schlae/cm5-reveng/BCM2712_HS.kicad_sch

## KiCad design BCM2712_HS.kicad_sch (2025-08-24)

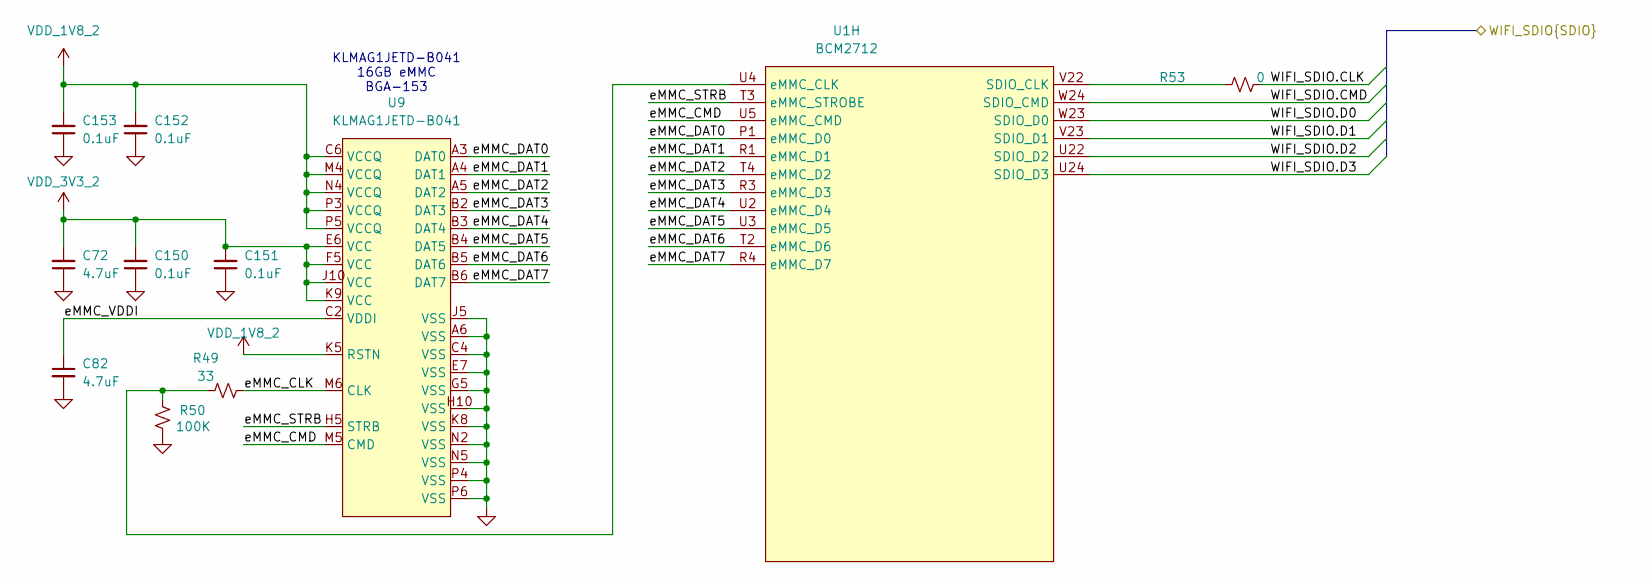
[picture p17: schematic BCM2712_HS.kicad_sch]

Parts:
C72, C82: 4.7uF; C_0402_1005Metric
C150, C151, C152, C153: 0.1uF; C_0201_0603Metric
R49: 33; R_0201_0603Metric
R50: 100K; R_0201_0603Metric
R53: 0; R_0201_0603Metric
U1: BCM2712; BGA-586_25x25_17.0x17.0mm
U9: KLMAG1JETD-B041; LFBGA-153_11.5x13mm_Layout14x14_P0.5mm

Connections:
GND: C72.1, C82.2, C150.1, C151.1, C152.1, C153.1, R50.2, U9.A6 (VSS), U9.C4 (VSS), U9.E7 (VSS), U9.G5 (VSS), U9.H10 (VSS), U9.J5 (VSS), U9.K8 (VSS), U9.N2 (VSS), U9.N5 (VSS), U9.P4 (VSS), U9.P6 (VSS)
unnamed: R49.2, R50.1, U1.U4 (eMMC_CLK)
unnamed: R53.1, U1.V22 (SDIO_CLK)
VDD_1V8_2: C152.2, C153.2, U9.C6 (VCCQ), U9.K5 (RSTN), U9.M4 (VCCQ), U9.N4 (VCCQ), U9.P3 (VCCQ), U9.P5 (VCCQ)
VDD_3V3_2: C72.2, C150.2, C151.2, U9.E6 (VCC), U9.F5 (VCC), U9.J10 (VCC), U9.K9 (VCC)
WIFI_SDIO.CLK: R53.2
WIFI_SDIO.CMD: U1.W24 (SDIO_CMD)
WIFI_SDIO.D0: U1.W23 (SDIO_D0)
WIFI_SDIO.D1: U1.V23 (SDIO_D1)
WIFI_SDIO.D2: U1.U22 (SDIO_D2)
WIFI_SDIO.D3: U1.U24 (SDIO_D3)
eMMC_CLK: R49.1, U9.M6 (CLK)
eMMC_CMD: U1.U5 (eMMC_CMD), U9.M5 (CMD)
eMMC_DAT0: U1.P1 (eMMC_D0), U9.A3 (DAT0)
eMMC_DAT1: U1.R1 (eMMC_D1), U9.A4 (DAT1)
eMMC_DAT2: U1.T4 (eMMC_D2), U9.A5 (DAT2)
eMMC_DAT3: U1.R3 (eMMC_D3), U9.B2 (DAT3)
eMMC_DAT4: U1.U2 (eMMC_D4), U9.B3 (DAT4)
eMMC_DAT5: U1.U3 (eMMC_D5), U9.B4 (DAT5)
eMMC_DAT6: U1.T2 (eMMC_D6), U9.B5 (DAT6)
eMMC_DAT7: U1.R4 (eMMC_D7), U9.B6 (DAT7)
eMMC_STRB: U1.T3 (eMMC_STROBE), U9.H5 (STRB)
eMMC_VDDI: C82.1, U9.C2 (VDDI)

Notes on the sheet:
KLMAG1JETD-B041 16GB eMMC BGA-153
