schlae/cm5-reveng/BCM2712_MISC.kicad_sch

## KiCad design BCM2712_MISC.kicad_sch (2025-08-24)

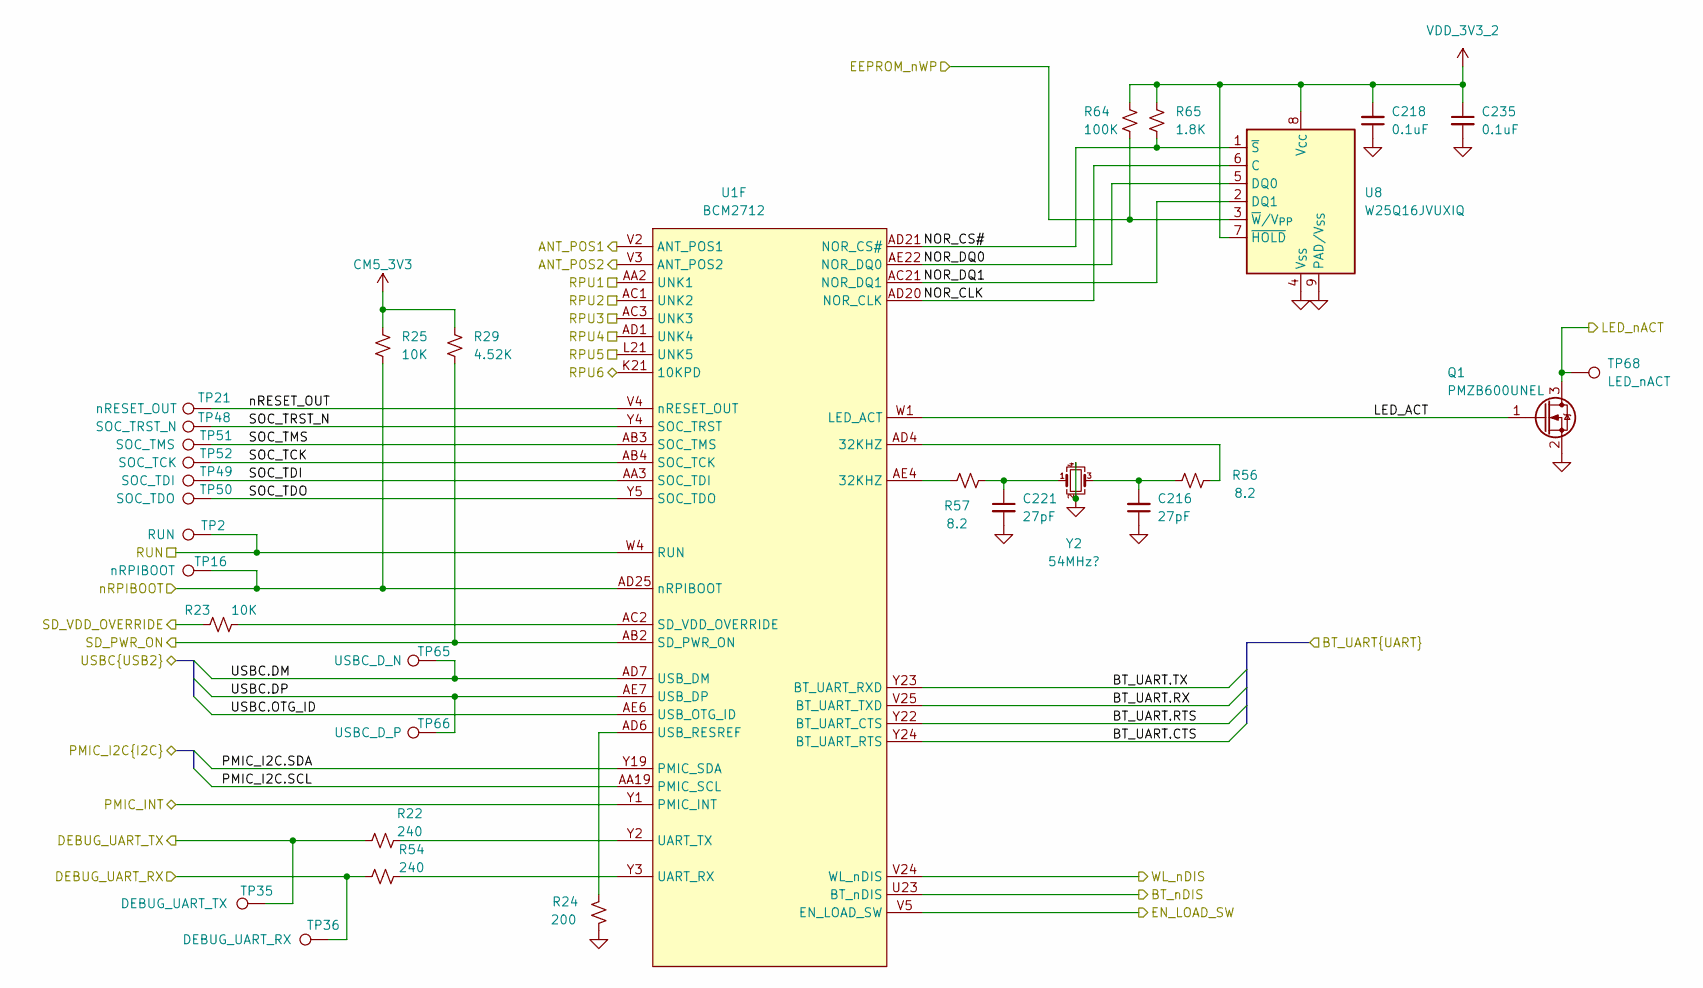
[picture p18: schematic BCM2712_MISC.kicad_sch]

Parts:
C216, C221: 27pF; C_0201_0603Metric
C218, C235: 0.1uF; C_0201_0603Metric
Q1: PMZB600UNEL; FEMTO_FET
R22, R54: 240; R_0201_0603Metric
R23, R25: 10K; R_0201_0603Metric
R24: 200; R_0201_0603Metric
R29: 4.52K; R_0201_0603Metric
R56, R57: 8.2; R_0201_0603Metric
R64: 100K; R_0201_0603Metric
R65: 1.8K; R_0201_0603Metric
TP2: RUN; TestPoint_Pad_D1.0mm
TP16: nRPIBOOT; TestPoint_Pad_D1.0mm
TP21: nRESET_OUT; TestPoint_Pad_D1.0mm
TP35: DEBUG_UART_TX; TestPoint_Pad_D1.0mm
TP36: DEBUG_UART_RX; TestPoint_Pad_D1.0mm
TP48: SOC_TRST_N; TestPoint_Pad_D1.0mm
TP49: SOC_TDI; TestPoint_Pad_D1.0mm
TP50: SOC_TDO; TestPoint_Pad_D1.0mm
TP51: SOC_TMS; TestPoint_Pad_D1.0mm
TP52: SOC_TCK; TestPoint_Pad_D1.0mm
TP65: USBC_D_N; TestPoint_Pad_D1.0mm
TP66: USBC_D_P; TestPoint_Pad_D1.0mm
TP68: LED_nACT; TestPoint_Pad_D1.0mm
U1: BCM2712; BGA-586_25x25_17.0x17.0mm
U8: W25Q16JVUXIQ; LFCSP-8-1EP_3x2mm_P0.5mm_EP1.6x0.25mm
Y2: 54MHz?; Oscillator_SMD_Abracon_ASE-4Pin_3.2x2.5mm

Connections:
ANT_POS1: U1.V2 (ANT_POS1)
ANT_POS2: U1.V3 (ANT_POS2)
BT_UART.CTS: U1.Y24 (BT_UART_RTS)
BT_UART.RTS: U1.Y22 (BT_UART_CTS)
BT_UART.RX: U1.V25 (BT_UART_TXD)
BT_UART.TX: U1.Y23 (BT_UART_RXD)
BT_nDIS: U1.U23 (BT_nDIS)
CM5_3V3: R25.1, R29.2
DEBUG_UART_RX: R54.1, TP36.1
DEBUG_UART_TX: R22.2, TP35.1
EEPROM_nWP: R64.1, U8.3 (~W/V_{PP})
EN_LOAD_SW: U1.V5 (EN_LOAD_SW)
GND: C216.1, C218.1, C221.2, C235.2, Q1.2 (S), R24.2, U8.4 (V_{SS}), U8.9 (PAD/V_{SS}), Y2.2, Y2.4
LED_ACT: Q1.1 (G), U1.W1 (LED_ACT)
LED_nACT: Q1.3 (D), TP68.1
NOR_CLK: U1.AD20 (NOR_CLK), U8.6 (C)
NOR_CS#: R65.1, U1.AD21 (NOR_CS#), U8.1 (~S)
NOR_DQ0: U1.AE22 (NOR_DQ0), U8.5 (DQ0)
NOR_DQ1: U1.AC21 (NOR_DQ1), U8.2 (DQ1)
unnamed: C216.2, R56.1, Y2.3
unnamed: C221.1, R57.1, Y2.1
unnamed: R22.1, U1.Y2 (UART_TX)
unnamed: R23.1, U1.AC2 (SD_VDD_OVERRIDE)
unnamed: R24.1, U1.AD6 (USB_RESREF)
unnamed: R54.2, U1.Y3 (UART_RX)
unnamed: R56.2, U1.AD4 (32KHZ)
unnamed: R57.2, U1.AE4 (32KHZ)
PMIC_I2C.SCL: U1.AA19 (PMIC_SCL)
PMIC_I2C.SDA: U1.Y19 (PMIC_SDA)
PMIC_INT: U1.Y1 (PMIC_INT)
RPU1: U1.AA2 (UNK1)
RPU2: U1.AC1 (UNK2)
RPU3: U1.AC3 (UNK3)
RPU4: U1.AD1 (UNK4)
RPU5: U1.L21 (UNK5)
RPU6: U1.K21 (10KPD)
RUN: TP2.1, U1.W4 (RUN)
SD_PWR_ON: R29.1, U1.AB2 (SD_PWR_ON)
SD_VDD_OVERRIDE: R23.2
SOC_TCK: TP52.1, U1.AB4 (SOC_TCK)
SOC_TDI: TP49.1, U1.AA3 (SOC_TDI)
SOC_TDO: TP50.1, U1.Y5 (SOC_TDO)
SOC_TMS: TP51.1, U1.AB3 (SOC_TMS)
SOC_TRST_N: TP48.1, U1.Y4 (SOC_TRST)
USBC.DM: TP65.1, U1.AD7 (USB_DM)
USBC.DP: TP66.1, U1.AE7 (USB_DP)
USBC.OTG_ID: U1.AE6 (USB_OTG_ID)
VDD_3V3_2: C218.2, C235.1, R64.2, R65.2, U8.7 (~HOLD), U8.8 (V_{CC})
WL_nDIS: U1.V24 (WL_nDIS)
nRESET_OUT: TP21.1, U1.V4 (nRESET_OUT)
nRPIBOOT: R25.2, TP16.1, U1.AD25 (nRPIBOOT)
