schlae/cm5-reveng/BCM2712_PWR2.kicad_sch

## KiCad design BCM2712_PWR2.kicad_sch (2025-08-24)

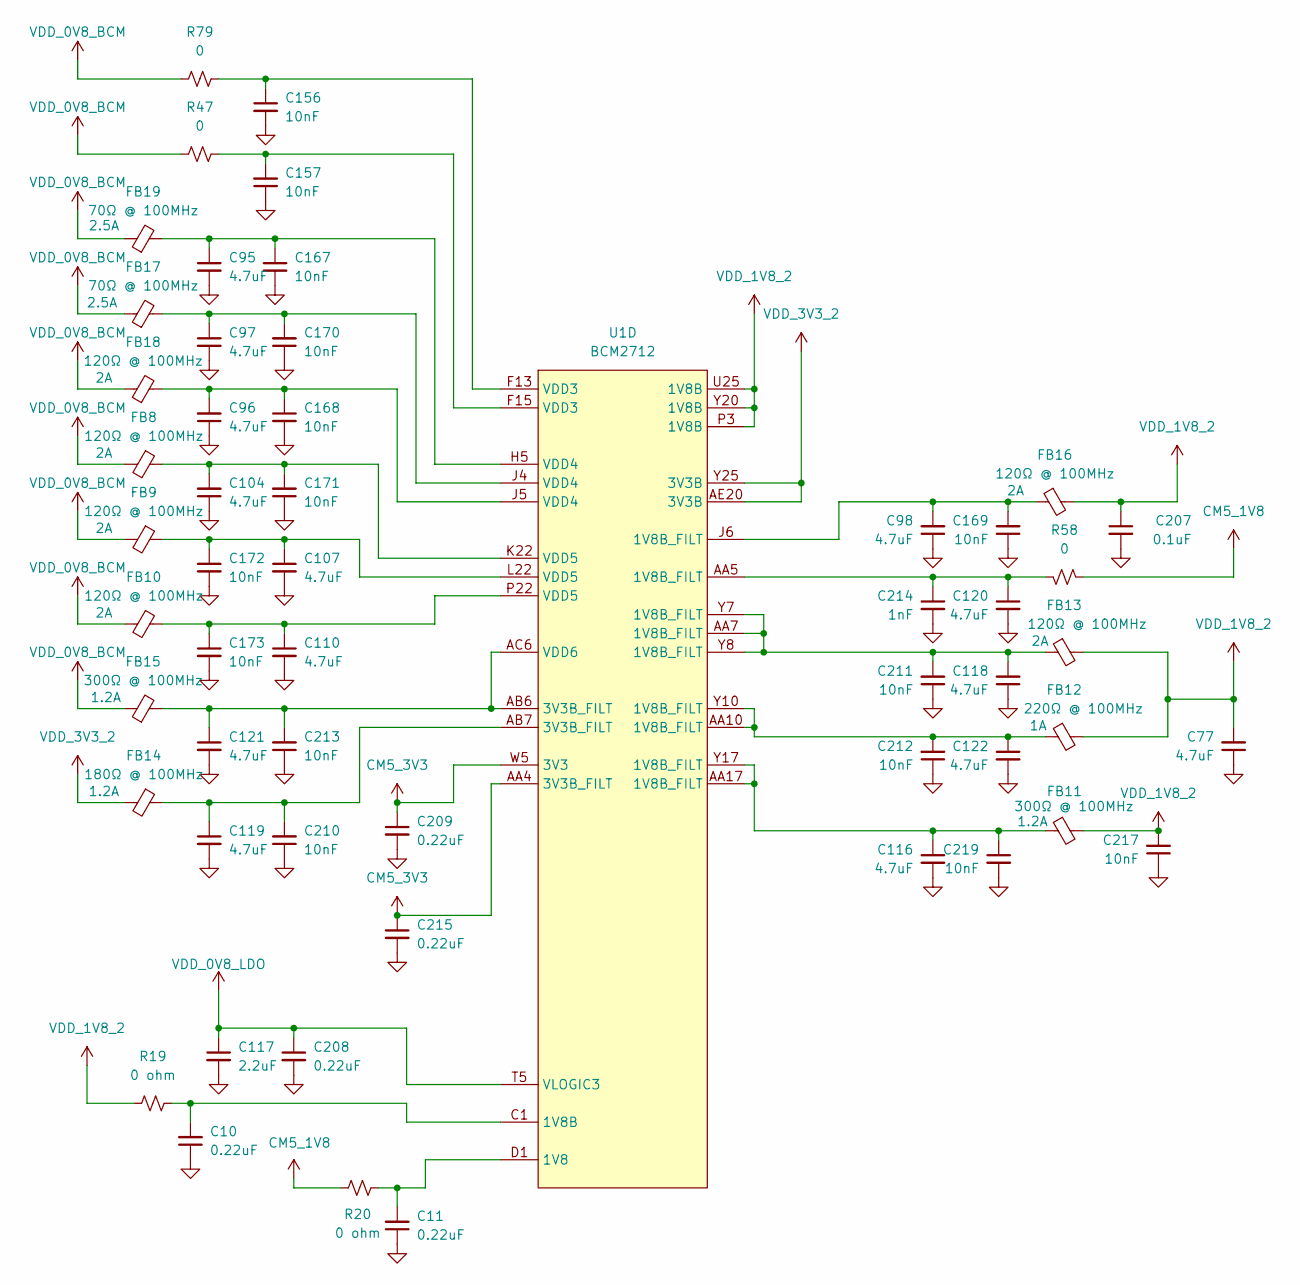
[picture p19: schematic BCM2712_PWR2.kicad_sch]

Parts:
C10, C11, C208, C209, C215: 0.22uF; C_0201_0603Metric
C77, C95, C96, C97, C98, C104, C107, C110, C116, C118, C119, C120, C121, C122: 4.7uF; C_0402_1005Metric
C117: 2.2uF; C_0402_1005Metric
C156, C157, C167, C168, C169, C170, C171, C172, C173, C210, C211, C212, C213, C217, C219: 10nF; C_0201_0603Metric
C207: 0.1uF; C_0201_0603Metric
C214: 1nF; C_0201_0603Metric
FB8, FB9, FB10, FB13, FB16, FB18: 120Ω @ 100MHz; L_0402_1005Metric; Rating 2A
FB11, FB15: 300Ω @ 100MHz; L_0402_1005Metric; Rating 1.2A
FB12: 220Ω @ 100MHz; L_0402_1005Metric; Rating 1A
FB14: 180Ω @ 100MHz; L_0402_1005Metric; Rating 1.2A
FB17, FB19: 70Ω @ 100MHz; L_0402_1005Metric; Rating 2.5A
R19, R20: 0 ohm; R_0201_0603Metric
R47, R58, R79: 0; R_0201_0603Metric
U1: BCM2712; BGA-586_25x25_17.0x17.0mm

Connections:
CM5_1V8: R20.2, R58.2
CM5_3V3: C209.1, C215.1, U1.AA4 (3V3B_FILT), U1.W5 (3V3)
GND: C10.1, C11.1, C77.1, C95.2, C96.1, C97.2, C98.1, C104.1, C107.2, C110.2, C116.2, C117.2, C118.1, C119.2, C120.2, C121.2, C122.2, C156.2, C157.1, C167.2, C168.2, C169.1, C170.1, C171.1, C172.2, C173.2, C207.2, C208.2, C209.2, C210.1, C211.1, C212.1, C213.1, C214.2, C215.2, C217.1, C219.2
unnamed: C10.2, R19.1, U1.C1 (1V8B)
unnamed: C11.2, R20.1, U1.D1 (1V8)
unnamed: C104.2, C171.2, FB8.1, U1.K22 (VDD5)
unnamed: C107.1, C172.1, FB9.1, U1.L22 (VDD5)
unnamed: C110.1, C173.1, FB10.1, U1.P22 (VDD5)
unnamed: C116.1, C219.1, FB11.1, U1.AA17 (1V8B_FILT), U1.Y17 (1V8B_FILT)
unnamed: C118.2, C211.2, FB13.1, U1.AA7 (1V8B_FILT), U1.Y7 (1V8B_FILT), U1.Y8 (1V8B_FILT)
unnamed: C119.1, C210.2, FB14.1, U1.AB7 (3V3B_FILT)
unnamed: C120.1, C214.1, R58.1, U1.AA5 (1V8B_FILT)
unnamed: C121.1, C213.2, FB15.2, U1.AB6 (3V3B_FILT), U1.AC6 (VDD6)
unnamed: C122.1, C212.2, FB12.1, U1.AA10 (1V8B_FILT), U1.Y10 (1V8B_FILT)
unnamed: C156.1, R79.1, U1.F13 (VDD3)
unnamed: C157.2, R47.1, U1.F15 (VDD3)
unnamed: C95.1, C167.1, FB19.2, U1.H5 (VDD4)
unnamed: C96.2, C168.1, FB18.2, U1.J5 (VDD4)
unnamed: C98.2, C169.2, FB16.1, U1.J6 (1V8B_FILT)
unnamed: C97.1, C170.2, FB17.2, U1.J4 (VDD4)
VDD_0V8_BCM: FB8.2, FB9.2, FB10.2, FB15.1, FB17.1, FB18.1, FB19.1, R47.2, R79.2
VDD_0V8_LDO: C117.1, C208.1, U1.T5 (VLOGIC3)
VDD_1V8_2: C77.2, C207.1, C217.2, FB11.2, FB12.2, FB13.2, FB16.2, R19.2, U1.P3 (1V8B), U1.U25 (1V8B), U1.Y20 (1V8B)
VDD_3V3_2: FB14.2, U1.AE20 (3V3B), U1.Y25 (3V3B)
