schlae/cm5-reveng/BCM2712_PWR.kicad_sch

## KiCad design BCM2712_PWR.kicad_sch (2025-08-24)

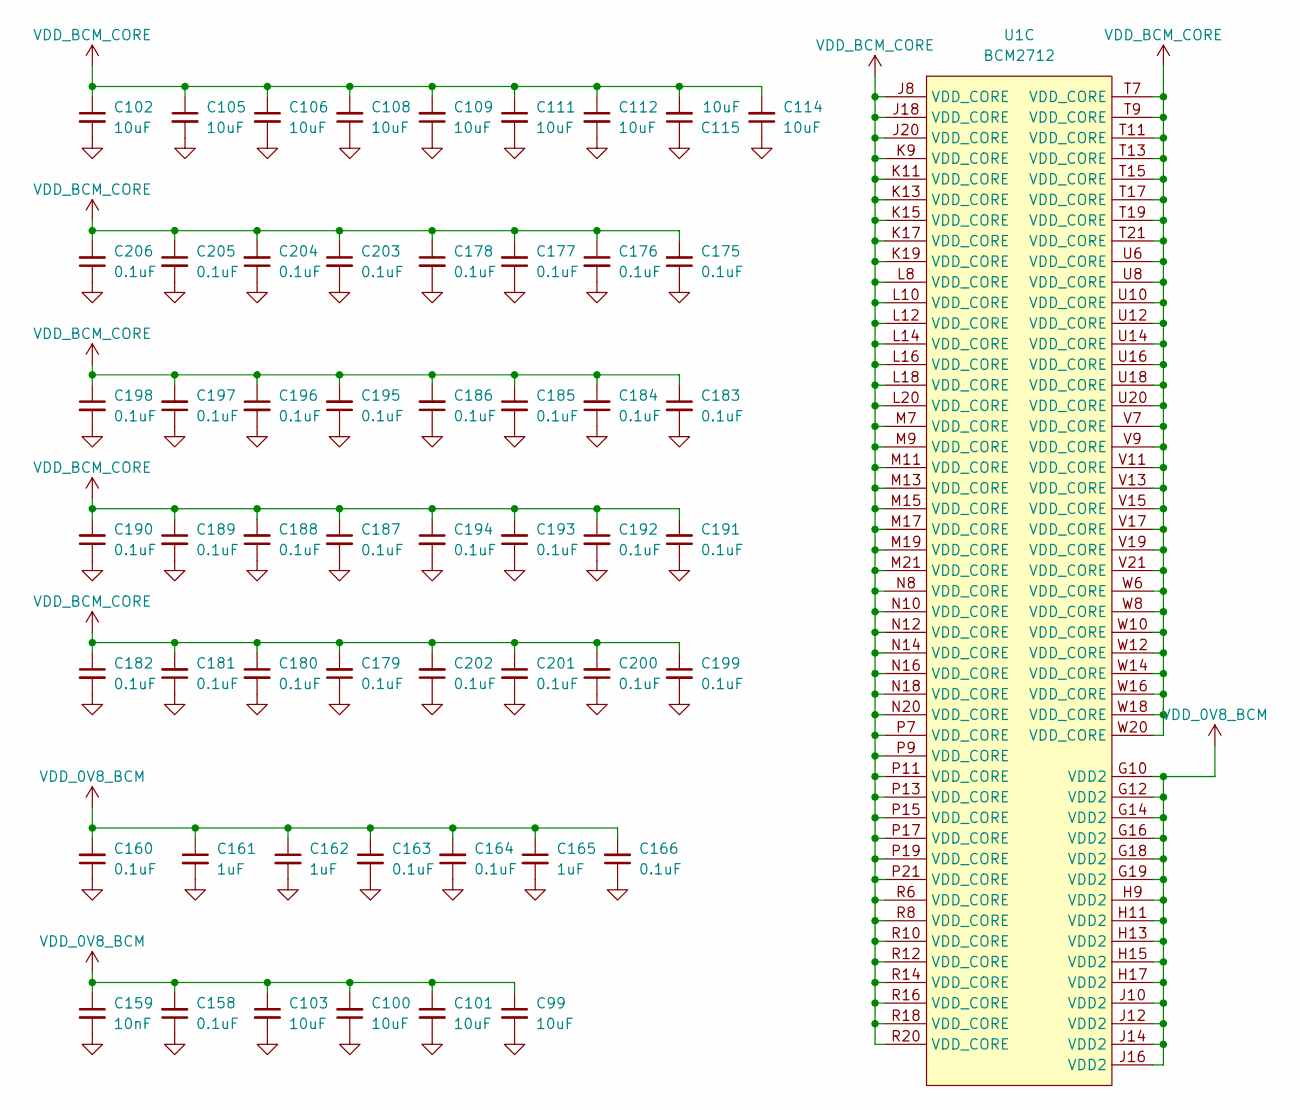
[picture p20: schematic BCM2712_PWR.kicad_sch]

Parts:
C99, C100, C101, C102, C103, C105, C106, C108, C109, C111, C112, C114, C115: 10uF; C_0402_1005Metric
C158, C160, C163, C164, C166, C175, C176, C177, C178, C179, C180, C181, C182, C183, C184, C185, C186, C187, C188, C189, C190, C191, C192, C193, C194, C195, C196, C197, C198, C199, C200, C201, C202, C203, C204, C205, C206: 0.1uF; C_0201_0603Metric
C159: 10nF; C_0201_0603Metric
C161, C162, C165: 1uF; C_0201_0603Metric
U1: BCM2712; BGA-586_25x25_17.0x17.0mm

Connections:
GND: C99.2, C100.1, C101.2, C102.2, C103.2, C105.2, C106.2, C108.1, C109.1, C111.2, C112.2, C114.1, C115.1, C158.1, C159.2, C160.1, C161.2, C162.2, C163.2, C164.1, C165.2, C166.1, C175.1, C176.2, C177.1, C178.2, C179.1, C180.2, C181.1, C182.2, C183.2, C184.1, C185.2, C186.1, C187.2, C188.1, C189.2, C190.1, C191.1, C192.2, C193.1, C194.2, C195.1, C196.2, C197.1, C198.2, C199.2, C200.1, C201.2, C202.1, C203.2, C204.1, C205.2, C206.1
VDD_0V8_BCM: C99.1, C100.2, C101.1, C103.1, C158.2, C159.1, C160.2, C161.1, C162.1, C163.1, C164.2, C165.1, C166.2, U1.G10 (VDD2), U1.G12 (VDD2), U1.G14 (VDD2), U1.G16 (VDD2), U1.G18 (VDD2), U1.G19 (VDD2), U1.H9 (VDD2), U1.H11 (VDD2), U1.H13 (VDD2), U1.H15 (VDD2), U1.H17 (VDD2), U1.J10 (VDD2), U1.J12 (VDD2), U1.J14 (VDD2), U1.J16 (VDD2)
VDD_BCM_CORE: C102.1, C105.1, C106.1, C108.2, C109.2, C111.1, C112.1, C114.2, C115.2, C175.2, C176.1, C177.2, C178.1, C179.2, C180.1, C181.2, C182.1, C183.1, C184.2, C185.1, C186.2, C187.1, C188.2, C189.1, C190.2, C191.2, C192.1, C193.2, C194.1, C195.2, C196.1, C197.2, C198.1, C199.1, C200.2, C201.1, C202.2, C203.1, C204.2, C205.1, C206.2, U1.J8 (VDD_CORE), U1.J18 (VDD_CORE), U1.J20 (VDD_CORE), U1.K9 (VDD_CORE), U1.K11 (VDD_CORE), U1.K13 (VDD_CORE), U1.K15 (VDD_CORE), U1.K17 (VDD_CORE), U1.K19 (VDD_CORE), U1.L8 (VDD_CORE), U1.L10 (VDD_CORE), U1.L12 (VDD_CORE), U1.L14 (VDD_CORE), U1.L16 (VDD_CORE), U1.L18 (VDD_CORE), U1.L20 (VDD_CORE), U1.M7 (VDD_CORE), U1.M9 (VDD_CORE), U1.M11 (VDD_CORE), U1.M13 (VDD_CORE), U1.M15 (VDD_CORE), U1.M17 (VDD_CORE), U1.M19 (VDD_CORE), U1.M21 (VDD_CORE), U1.N8 (VDD_CORE), U1.N10 (VDD_CORE), U1.N12 (VDD_CORE), U1.N14 (VDD_CORE), U1.N16 (VDD_CORE), U1.N18 (VDD_CORE), U1.N20 (VDD_CORE), U1.P7 (VDD_CORE), U1.P9 (VDD_CORE), U1.P11 (VDD_CORE), U1.P13 (VDD_CORE), U1.P15 (VDD_CORE), U1.P17 (VDD_CORE), U1.P19 (VDD_CORE), U1.P21 (VDD_CORE), U1.R6 (VDD_CORE), U1.R8 (VDD_CORE), U1.R10 (VDD_CORE), U1.R12 (VDD_CORE), U1.R14 (VDD_CORE), U1.R16 (VDD_CORE), U1.R18 (VDD_CORE), U1.R20 (VDD_CORE), U1.T7 (VDD_CORE), U1.T9 (VDD_CORE), U1.T11 (VDD_CORE), U1.T13 (VDD_CORE), U1.T15 (VDD_CORE), U1.T17 (VDD_CORE), U1.T19 (VDD_CORE), U1.T21 (VDD_CORE), U1.U6 (VDD_CORE), U1.U8 (VDD_CORE), U1.U10 (VDD_CORE), U1.U12 (VDD_CORE), U1.U14 (VDD_CORE), U1.U16 (VDD_CORE), U1.U18 (VDD_CORE), U1.U20 (VDD_CORE), U1.V7 (VDD_CORE), U1.V9 (VDD_CORE), U1.V11 (VDD_CORE), U1.V13 (VDD_CORE), U1.V15 (VDD_CORE), U1.V17 (VDD_CORE), U1.V19 (VDD_CORE), U1.V21 (VDD_CORE), U1.W6 (VDD_CORE), U1.W8 (VDD_CORE), U1.W10 (VDD_CORE), U1.W12 (VDD_CORE), U1.W14 (VDD_CORE), U1.W16 (VDD_CORE), U1.W18 (VDD_CORE), U1.W20 (VDD_CORE)
