schlae/cm5-reveng/CM5RevEng.kicad_sch

## KiCad design CM5RevEng.kicad_sch (2025-08-24)

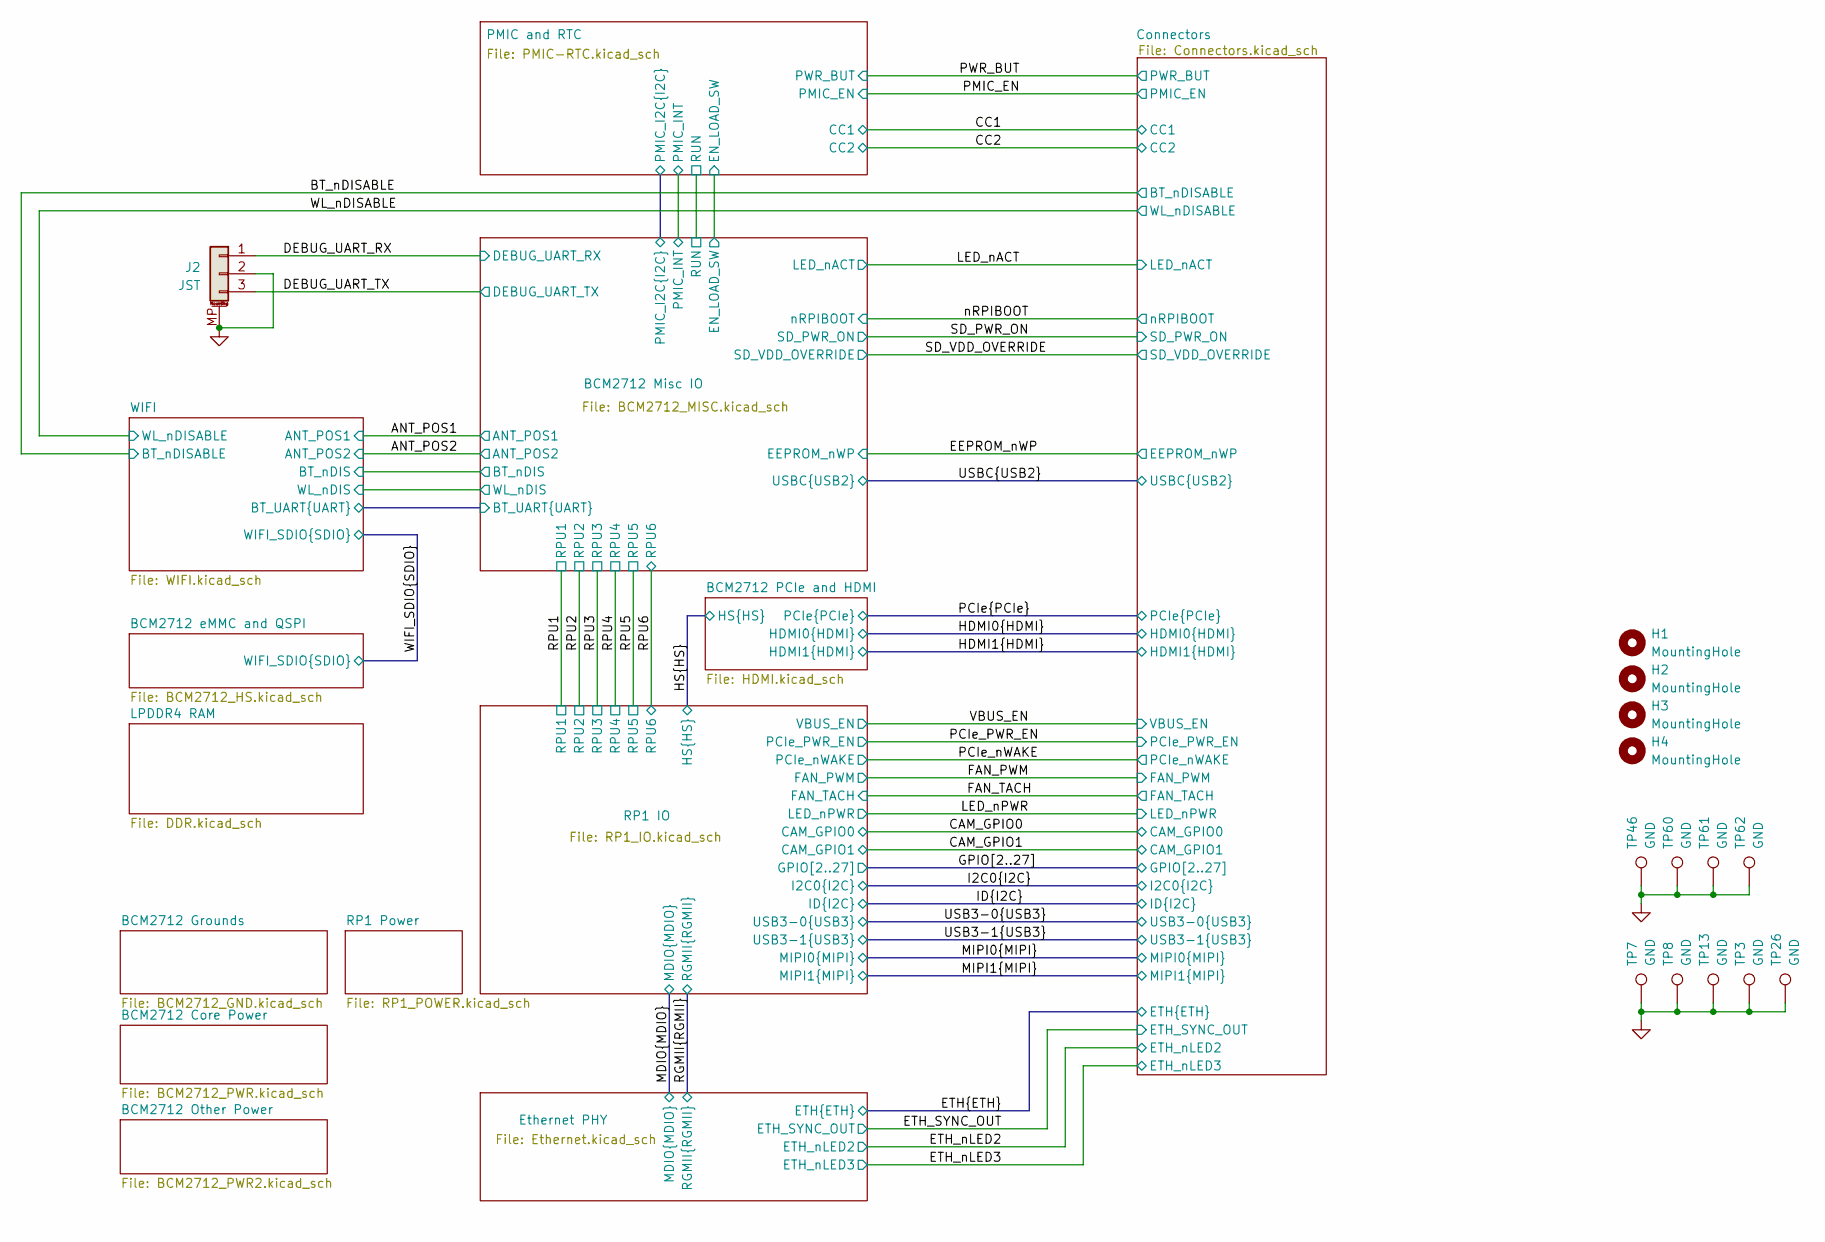
[picture p21: schematic CM5RevEng.kicad_sch]

Parts:
H1, H2, H3, H4: MountingHole; CM5_MH
J2: JST; JST_SH_BM03B-SRSS-TB_1x03-1MP_P1.00mm_Vertical
TP3, TP7, TP8, TP13, TP26, TP46, TP60, TP61, TP62: GND; TestPoint_Pad_D1.0mm

Connections:
DEBUG_UART_RX: J2.1
DEBUG_UART_TX: J2.3
GND: J2.2, J2.MP (MountPin), TP3.1, TP7.1, TP8.1, TP13.1, TP26.1, TP46.1, TP60.1, TP61.1, TP62.1
