schlae/cm5-reveng/Connectors.kicad_sch

## KiCad design Connectors.kicad_sch (2025-08-24)

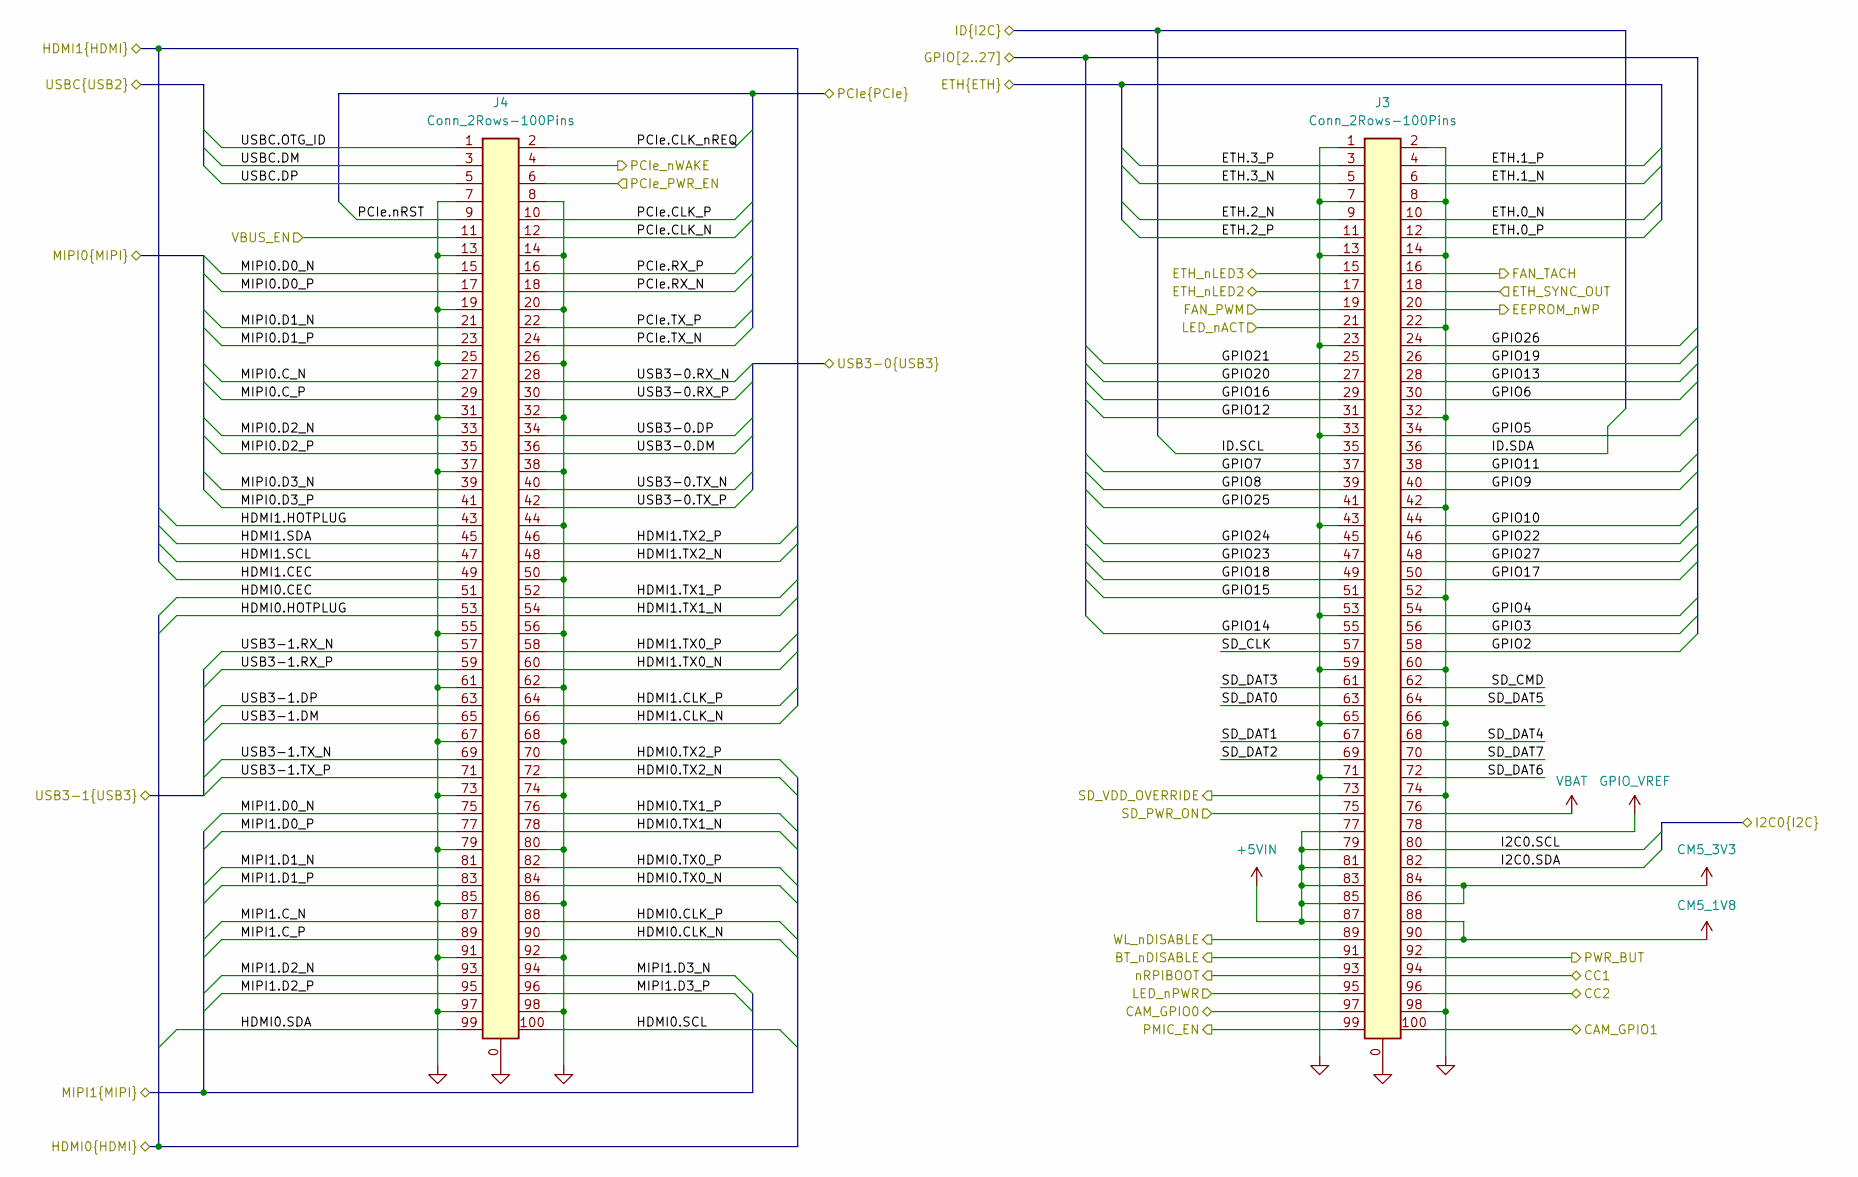
[picture p22: schematic Connectors.kicad_sch]

Parts:
J3, J4: Conn_2Rows-100Pins; 10164228-1001A1RLF

Connections:
+5VIN: J3.77, J3.79, J3.81, J3.83, J3.85, J3.87
BT_nDISABLE: J3.91
CAM_GPIO0: J3.97
CAM_GPIO1: J3.100
CC1: J3.94
CC2: J3.96
CM5_1V8: J3.88, J3.90
CM5_3V3: J3.84, J3.86
EEPROM_nWP: J3.20
ETH.0_N: J3.10
ETH.0_P: J3.12
ETH.1_N: J3.6
ETH.1_P: J3.4
ETH.2_N: J3.9
ETH.2_P: J3.11
ETH.3_N: J3.5
ETH.3_P: J3.3
ETH_SYNC_OUT: J3.18
ETH_nLED2: J3.17
ETH_nLED3: J3.15
FAN_PWM: J3.19
FAN_TACH: J3.16
GND: J3.0 (SH), J3.1, J3.2, J3.7, J3.8, J3.13, J3.14, J3.22, J3.23, J3.32, J3.33, J3.42, J3.43, J3.52, J3.53, J3.59, J3.60, J3.65, J3.66, J3.71, J3.74, J3.98, J4.0 (SH), J4.7, J4.8, J4.13, J4.14, J4.19, J4.20, J4.25, J4.26, J4.31, J4.32, J4.37, J4.38, J4.44, J4.50, J4.55, J4.56, J4.61, J4.62, J4.67, J4.68, J4.73, J4.74, J4.79, J4.80, J4.85, J4.86, J4.91, J4.92, J4.97, J4.98
GPIO2: J3.58
GPIO3: J3.56
GPIO4: J3.54
GPIO5: J3.34
GPIO6: J3.30
GPIO7: J3.37
GPIO8: J3.39
GPIO9: J3.40
GPIO10: J3.44
GPIO11: J3.38
GPIO12: J3.31
GPIO13: J3.28
GPIO14: J3.55
GPIO15: J3.51
GPIO16: J3.29
GPIO17: J3.50
GPIO18: J3.49
GPIO19: J3.26
GPIO20: J3.27
GPIO21: J3.25
GPIO22: J3.46
GPIO23: J3.47
GPIO24: J3.45
GPIO25: J3.41
GPIO26: J3.24
GPIO27: J3.48
GPIO_VREF: J3.78
HDMI0.CEC: J4.51
HDMI0.CLK_N: J4.90
HDMI0.CLK_P: J4.88
HDMI0.HOTPLUG: J4.53
HDMI0.SCL: J4.100
HDMI0.SDA: J4.99
HDMI0.TX0_N: J4.84
HDMI0.TX0_P: J4.82
HDMI0.TX1_N: J4.78
HDMI0.TX1_P: J4.76 (Pin_74)
HDMI0.TX2_N: J4.72
HDMI0.TX2_P: J4.70
HDMI1.CEC: J4.49
HDMI1.CLK_N: J4.66
HDMI1.CLK_P: J4.64
HDMI1.HOTPLUG: J4.43
HDMI1.SCL: J4.47
HDMI1.SDA: J4.45
HDMI1.TX0_N: J4.60
HDMI1.TX0_P: J4.58
HDMI1.TX1_N: J4.54
HDMI1.TX1_P: J4.52
HDMI1.TX2_N: J4.48
HDMI1.TX2_P: J4.46
I2C0.SCL: J3.80
I2C0.SDA: J3.82
ID.SCL: J3.35
ID.SDA: J3.36
LED_nACT: J3.21
LED_nPWR: J3.95
MIPI0.C_N: J4.27
MIPI0.C_P: J4.29
MIPI0.D0_N: J4.15
MIPI0.D0_P: J4.17
MIPI0.D1_N: J4.21
MIPI0.D1_P: J4.23
MIPI0.D2_N: J4.33
MIPI0.D2_P: J4.35
MIPI0.D3_N: J4.39
MIPI0.D3_P: J4.41
MIPI1.C_N: J4.87
MIPI1.C_P: J4.89
MIPI1.D0_N: J4.75
MIPI1.D0_P: J4.77
MIPI1.D1_N: J4.81
MIPI1.D1_P: J4.83
MIPI1.D2_N: J4.93
MIPI1.D2_P: J4.95
MIPI1.D3_N: J4.94
MIPI1.D3_P: J4.96
PCIe.CLK_N: J4.12
PCIe.CLK_P: J4.10
PCIe.CLK_nREQ: J4.2
PCIe.RX_N: J4.18
PCIe.RX_P: J4.16
PCIe.TX_N: J4.24
PCIe.TX_P: J4.22
PCIe.nRST: J4.9
PCIe_PWR_EN: J4.6
PCIe_nWAKE: J4.4
PMIC_EN: J3.99
PWR_BUT: J3.92
SD_CLK: J3.57
SD_CMD: J3.62
SD_DAT0: J3.63
SD_DAT1: J3.67
SD_DAT2: J3.69
SD_DAT3: J3.61
SD_DAT4: J3.68
SD_DAT5: J3.64
SD_DAT6: J3.72
SD_DAT7: J3.70
SD_PWR_ON: J3.75
SD_VDD_OVERRIDE: J3.73
USB3-0.DM: J4.36
USB3-0.DP: J4.34
USB3-0.RX_N: J4.28
USB3-0.RX_P: J4.30
USB3-0.TX_N: J4.40
USB3-0.TX_P: J4.42
USB3-1.DM: J4.65
USB3-1.DP: J4.63
USB3-1.RX_N: J4.57
USB3-1.RX_P: J4.59
USB3-1.TX_N: J4.69
USB3-1.TX_P: J4.71
USBC.DM: J4.3
USBC.DP: J4.5
USBC.OTG_ID: J4.1
VBAT: J3.76 (Pin_74)
VBUS_EN: J4.11
WL_nDISABLE: J3.89
nRPIBOOT: J3.93
