schlae/cm5-reveng/DDR.kicad_sch

## KiCad design DDR.kicad_sch (2025-08-24)

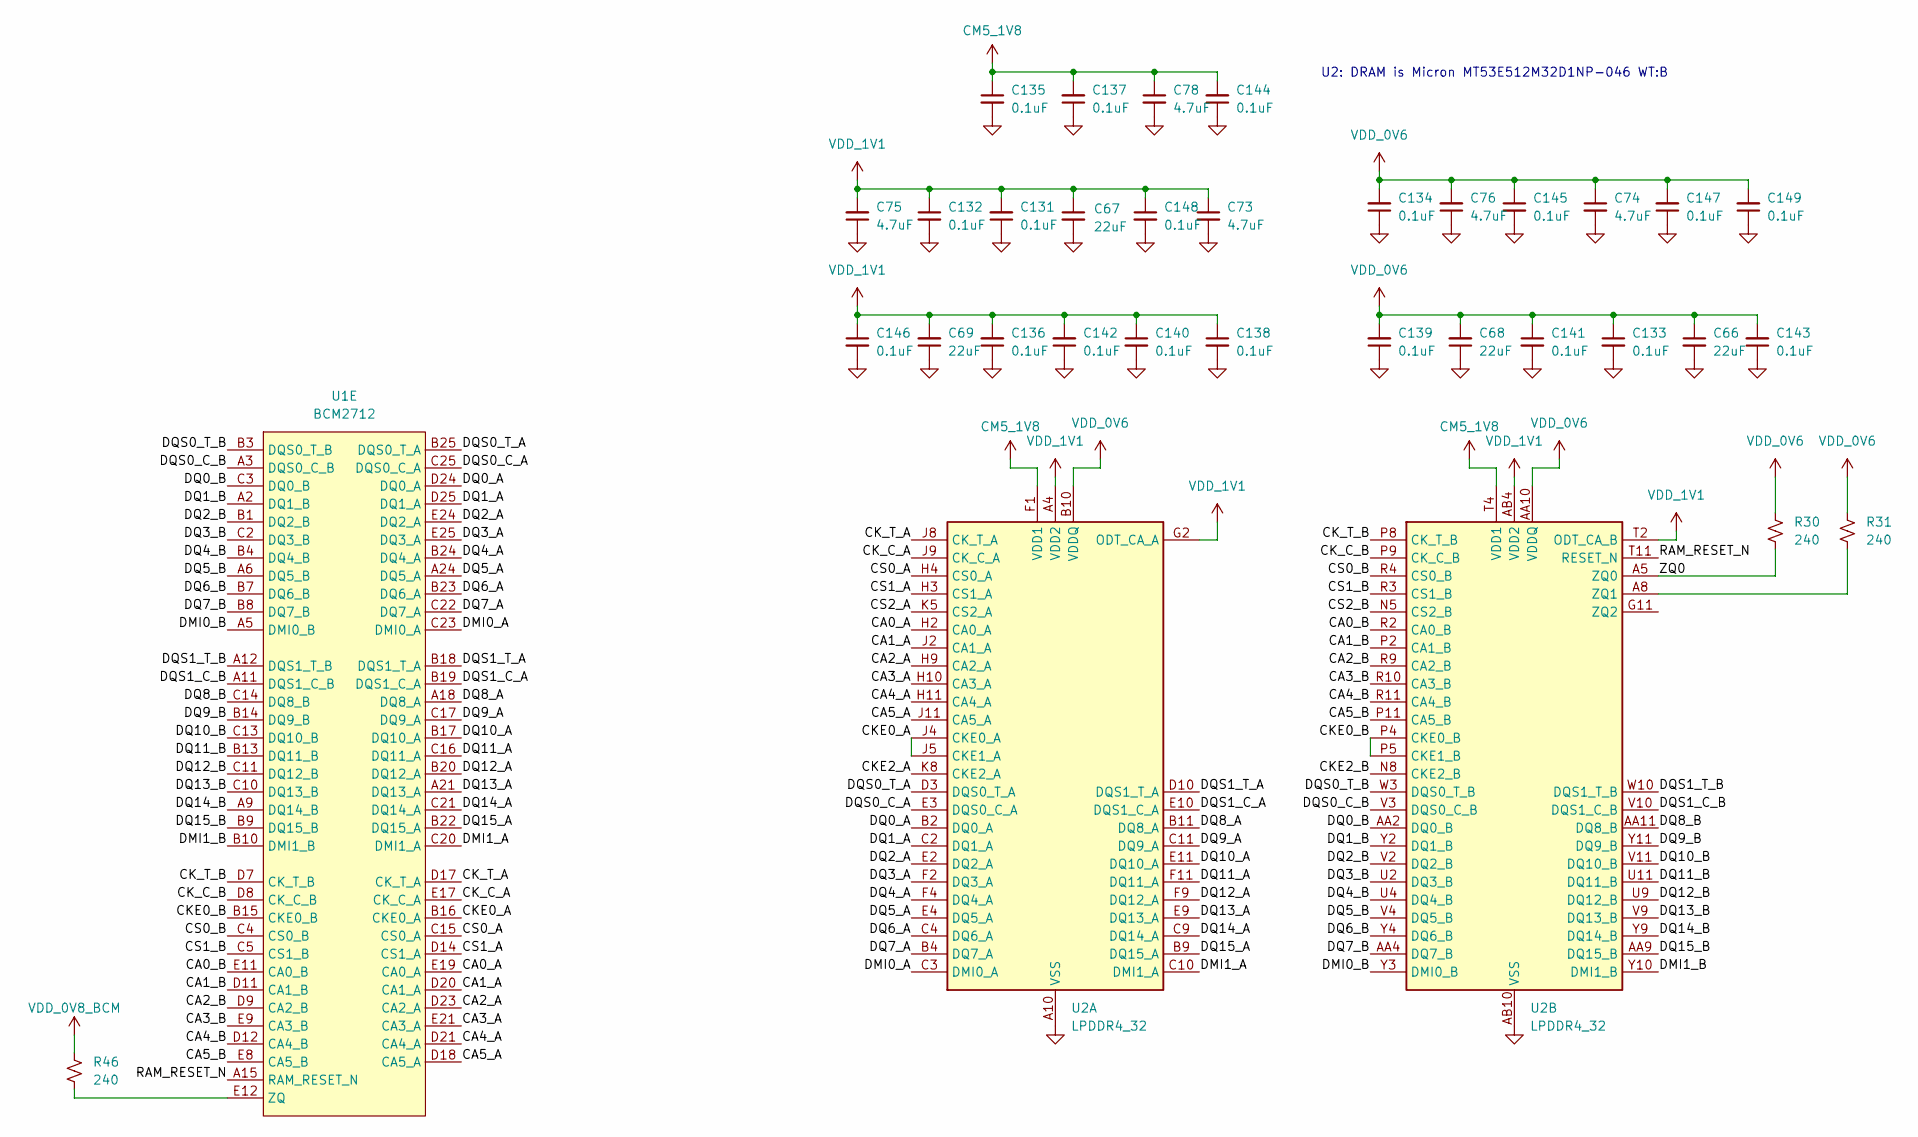
[picture p23: schematic DDR.kicad_sch]

Parts:
C66, C67, C68, C69: 22uF; C_0603_1608Metric
C73, C74, C75, C76, C78: 4.7uF; C_0402_1005Metric
C131, C132, C133, C134, C135, C136, C137, C138, C139, C140, C141, C142, C143, C144, C145, C146, C147, C148, C149: 0.1uF; C_0201_0603Metric
R30, R31, R46: 240; R_0201_0603Metric
U1: BCM2712; BGA-586_25x25_17.0x17.0mm
U2: LPDDR4_32; BGA-200_10x14.5mm_Layout12x22_P0.8x0.65mm

Connections:
CA0_A: U1.E19 (CA0_A), U2.H2 (CA0_A)
CA0_B: U1.E11 (CA0_B), U2.R2 (CA0_B)
CA1_A: U1.D20 (CA1_A), U2.J2 (CA1_A)
CA1_B: U1.D11 (CA1_B), U2.P2 (CA1_B)
CA2_A: U1.D23 (CA2_A), U2.H9 (CA2_A)
CA2_B: U1.D9 (CA2_B), U2.R9 (CA2_B)
CA3_A: U1.E21 (CA3_A), U2.H10 (CA3_A)
CA3_B: U1.E9 (CA3_B), U2.R10 (CA3_B)
CA4_A: U1.D21 (CA4_A), U2.H11 (CA4_A)
CA4_B: U1.D12 (CA4_B), U2.R11 (CA4_B)
CA5_A: U1.D18 (CA5_A), U2.J11 (CA5_A)
CA5_B: U1.E8 (CA5_B), U2.P11 (CA5_B)
CKE0_A: U1.B16 (CKE0_A), U2.J4 (CKE0_A), U2.J5 (CKE1_A)
CKE0_B: U1.B15 (CKE0_B), U2.P4 (CKE0_B), U2.P5 (CKE1_B)
CKE2_A: U2.K8 (CKE2_A)
CKE2_B: U2.N8 (CKE2_B)
CK_C_A: U1.E17 (CK_C_A), U2.J9 (CK_C_A)
CK_C_B: U1.D8 (CK_C_B), U2.P9 (CK_C_B)
CK_T_A: U1.D17 (CK_T_A), U2.J8 (CK_T_A)
CK_T_B: U1.D7 (CK_T_B), U2.P8 (CK_T_B)
CM5_1V8: C78.1, C135.1, C137.2, C144.2, U2.F1 (VDD1), U2.F12 (VDD1), U2.G4 (VDD1), U2.G9 (VDD1), U2.T4 (VDD1), U2.T9 (VDD1), U2.U1 (VDD1), U2.U12 (VDD1)
CS0_A: U1.C15 (CS0_A), U2.H4 (CS0_A)
CS0_B: U1.C4 (CS0_B), U2.R4 (CS0_B)
CS1_A: U1.D14 (CS1_A), U2.H3 (CS1_A)
CS1_B: U1.C5 (CS1_B), U2.R3 (CS1_B)
CS2_A: U2.K5 (CS2_A)
CS2_B: U2.N5 (CS2_B)
DMI0_A: U1.C23 (DMI0_A), U2.C3 (DMI0_A)
DMI0_B: U1.A5 (DMI0_B), U2.Y3 (DMI0_B)
DMI1_A: U1.C20 (DMI1_A), U2.C10 (DMI1_A)
DMI1_B: U1.B10 (DMI1_B), U2.Y10 (DMI1_B)
DQ0_A: U1.D24 (DQ0_A), U2.B2 (DQ0_A)
DQ0_B: U1.C3 (DQ0_B), U2.AA2 (DQ0_B)
DQ1_A: U1.D25 (DQ1_A), U2.C2 (DQ1_A)
DQ1_B: U1.A2 (DQ1_B), U2.Y2 (DQ1_B)
DQ2_A: U1.E24 (DQ2_A), U2.E2 (DQ2_A)
DQ2_B: U1.B1 (DQ2_B), U2.V2 (DQ2_B)
DQ3_A: U1.E25 (DQ3_A), U2.F2 (DQ3_A)
DQ3_B: U1.C2 (DQ3_B), U2.U2 (DQ3_B)
DQ4_A: U1.B24 (DQ4_A), U2.F4 (DQ4_A)
DQ4_B: U1.B4 (DQ4_B), U2.U4 (DQ4_B)
DQ5_A: U1.A24 (DQ5_A), U2.E4 (DQ5_A)
DQ5_B: U1.A6 (DQ5_B), U2.V4 (DQ5_B)
DQ6_A: U1.B23 (DQ6_A), U2.C4 (DQ6_A)
DQ6_B: U1.B7 (DQ6_B), U2.Y4 (DQ6_B)
DQ7_A: U1.C22 (DQ7_A), U2.B4 (DQ7_A)
DQ7_B: U1.B8 (DQ7_B), U2.AA4 (DQ7_B)
DQ8_A: U1.A18 (DQ8_A), U2.B11 (DQ8_A)
DQ8_B: U1.C14 (DQ8_B), U2.AA11 (DQ8_B)
DQ9_A: U1.C17 (DQ9_A), U2.C11 (DQ9_A)
DQ9_B: U1.B14 (DQ9_B), U2.Y11 (DQ9_B)
DQ10_A: U1.B17 (DQ10_A), U2.E11 (DQ10_A)
DQ10_B: U1.C13 (DQ10_B), U2.V11 (DQ10_B)
DQ11_A: U1.C16 (DQ11_A), U2.F11 (DQ11_A)
DQ11_B: U1.B13 (DQ11_B), U2.U11 (DQ11_B)
DQ12_A: U1.B20 (DQ12_A), U2.F9 (DQ12_A)
DQ12_B: U1.C11 (DQ12_B), U2.U9 (DQ12_B)
DQ13_A: U1.A21 (DQ13_A), U2.E9 (DQ13_A)
DQ13_B: U1.C10 (DQ13_B), U2.V9 (DQ13_B)
DQ14_A: U1.C21 (DQ14_A), U2.C9 (DQ14_A)
DQ14_B: U1.A9 (DQ14_B), U2.Y9 (DQ14_B)
DQ15_A: U1.B22 (DQ15_A), U2.B9 (DQ15_A)
DQ15_B: U1.B9 (DQ15_B), U2.AA9 (DQ15_B)
DQS0_C_A: U1.C25 (DQS0_C_A), U2.E3 (DQS0_C_A)
DQS0_C_B: U1.A3 (DQS0_C_B), U2.V3 (DQS0_C_B)
DQS0_T_A: U1.B25 (DQS0_T_A), U2.D3 (DQS0_T_A)
DQS0_T_B: U1.B3 (DQS0_T_B), U2.W3 (DQS0_T_B)
DQS1_C_A: U1.B19 (DQS1_C_A), U2.E10 (DQS1_C_A)
DQS1_C_B: U1.A11 (DQS1_C_B), U2.V10 (DQS1_C_B)
DQS1_T_A: U1.B18 (DQS1_T_A), U2.D10 (DQS1_T_A)
DQS1_T_B: U1.A12 (DQS1_T_B), U2.W10 (DQS1_T_B)
GND: C66.2, C67.2, C68.1, C69.1, C73.2, C74.2, C75.1, C76.1, C78.2, C131.1, C132.2, C133.2, C134.1, C135.2, C136.1, C137.1, C138.2, C139.1, C140.2, C141.2, C142.1, C143.1, C144.1, C145.2, C146.2, C147.1, C148.2, C149.1, U2.A3 (VSS), U2.A10 (VSS), U2.AB3 (VSS), U2.AB5 (VSS), U2.AB8 (VSS), U2.AB10 (VSS), U2.C1 (VSS), U2.C5 (VSS), U2.C8 (VSS), U2.C12 (VSS), U2.D2 (VSS), U2.D4 (VSS), U2.D9 (VSS), U2.D11 (VSS), U2.E1 (VSS), U2.E5 (VSS), U2.E8 (VSS), U2.E12 (VSS), U2.G1 (VSS), U2.G3 (VSS), U2.G5 (VSS), U2.G8 (VSS), U2.G10 (VSS), U2.G12 (VSS), U2.J1 (VSS), U2.J3 (VSS), U2.J10 (VSS), U2.J12 (VSS), U2.K2 (VSS), U2.K4 (VSS), U2.K9 (VSS), U2.K11 (VSS), U2.N2 (VSS), U2.N4 (VSS), U2.N9 (VSS), U2.N11 (VSS), U2.P1 (VSS), U2.P3 (VSS), U2.P10 (VSS), U2.P12 (VSS), U2.T1 (VSS), U2.T3 (VSS), U2.T5 (VSS), U2.T8 (VSS), U2.T10 (VSS), U2.T12 (VSS), U2.V1 (VSS), U2.V5 (VSS), U2.V8 (VSS), U2.V12 (VSS), U2.W2 (VSS), U2.W4 (VSS), U2.W9 (VSS), U2.W11 (VSS), U2.Y1 (VSS), U2.Y5 (VSS), U2.Y8 (VSS), U2.Y12 (VSS)
unnamed: R31.2, U2.A8 (ZQ1)
unnamed: R46.2, U1.E12 (ZQ)
RAM_RESET_N: U1.A15 (RAM_RESET_N), U2.T11 (RESET_N)
VDD_0V6: C66.1, C68.2, C74.1, C76.2, C133.1, C134.2, C139.2, C141.1, C143.2, C145.1, C147.2, C149.2, R30.1, R31.1, U2.AA3 (VDDQ), U2.AA5 (VDDQ), U2.AA8 (VDDQ), U2.AA10 (VDDQ), U2.B3 (VDDQ), U2.B5 (VDDQ), U2.B8 (VDDQ), U2.B10 (VDDQ), U2.D1 (VDDQ), U2.D5 (VDDQ), U2.D8 (VDDQ), U2.D12 (VDDQ), U2.F3 (VDDQ), U2.F10 (VDDQ), U2.U3 (VDDQ), U2.U10 (VDDQ), U2.W1 (VDDQ), U2.W5 (VDDQ), U2.W8 (VDDQ), U2.W12 (VDDQ)
VDD_0V8_BCM: R46.1
VDD_1V1: C67.1, C69.2, C73.1, C75.2, C131.2, C132.1, C136.2, C138.1, C140.1, C142.2, C146.1, C148.1, U2.A4 (VDD2), U2.A9 (VDD2), U2.AB4 (VDD2), U2.AB9 (VDD2), U2.F5 (VDD2), U2.F8 (VDD2), U2.G2 (ODT_CA_A), U2.H1 (VDD2), U2.H5 (VDD2), U2.H8 (VDD2), U2.H12 (VDD2), U2.K1 (VDD2), U2.K3 (VDD2), U2.K10 (VDD2), U2.K12 (VDD2), U2.N1 (VDD2), U2.N3 (VDD2), U2.N10 (VDD2), U2.N12 (VDD2), U2.R1 (VDD2), U2.R5 (VDD2), U2.R8 (VDD2), U2.R12 (VDD2), U2.T2 (ODT_CA_B), U2.U5 (VDD2), U2.U8 (VDD2)
ZQ0: R30.2, U2.A5 (ZQ0)

Notes on the sheet:
U2: DRAM is Micron MT53E512M32D1NP-046 WT:B
