schlae/cm5-reveng/Ethernet.kicad_sch

## KiCad design Ethernet.kicad_sch (2025-08-24)

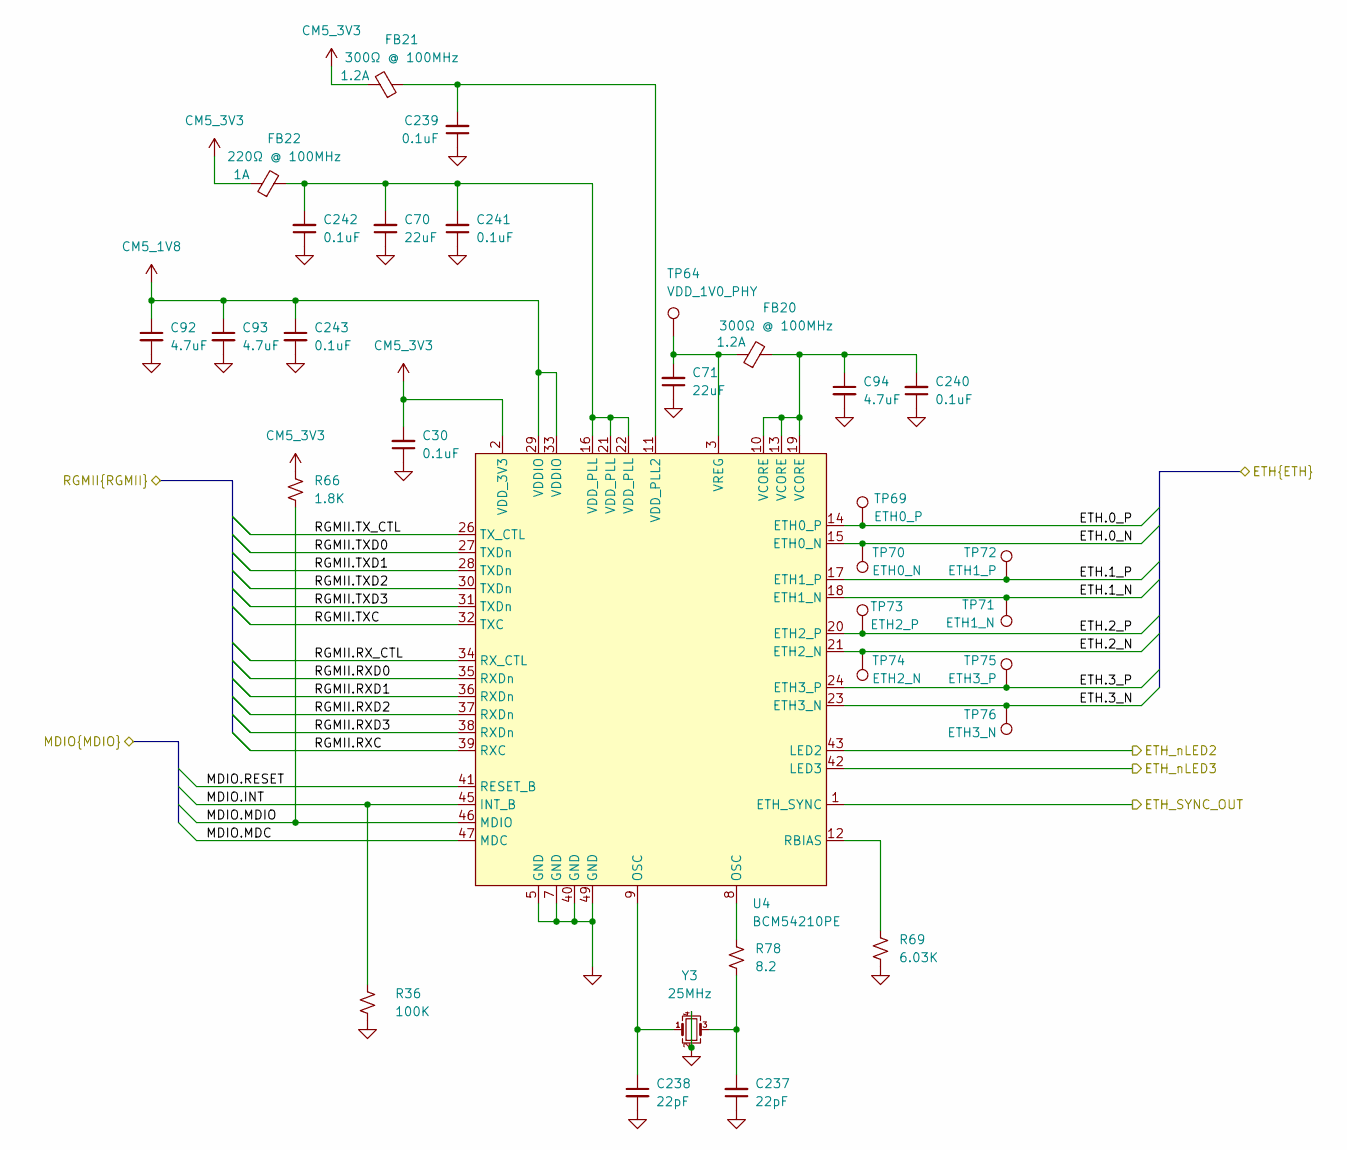
[picture p24: schematic Ethernet.kicad_sch]

Parts:
C30, C239, C240, C241, C242, C243: 0.1uF; C_0201_0603Metric
C70, C71: 22uF; C_0603_1608Metric
C92, C93, C94: 4.7uF; C_0402_1005Metric
C237, C238: 22pF; C_0201_0603Metric
FB20, FB21: 300Ω @ 100MHz; L_0402_1005Metric; Rating 1.2A
FB22: 220Ω @ 100MHz; L_0402_1005Metric; Rating 1A
R36: 100K; R_0201_0603Metric
R66: 1.8K; R_0201_0603Metric
R69: 6.03K; R_0201_0603Metric
R78: 8.2; R_0201_0603Metric
TP64: VDD_1V0_PHY; TestPoint_Pad_D1.0mm
TP69: ETH0_P; TestPoint_Pad_D1.0mm
TP70: ETH0_N; TestPoint_Pad_D1.0mm
TP71: ETH1_N; TestPoint_Pad_D1.0mm
TP72: ETH1_P; TestPoint_Pad_D1.0mm
TP73: ETH2_P; TestPoint_Pad_D1.0mm
TP74: ETH2_N; TestPoint_Pad_D1.0mm
TP75: ETH3_P; TestPoint_Pad_D1.0mm
TP76: ETH3_N; TestPoint_Pad_D1.0mm
U4: BCM54210PE; TQFN-48-1EP_7x7mm_P0.5mm_EP5.1x5.1mm
Y3: 25MHz; Crystal_SMD_1210-4Pin_1.2x1.0mm

Connections:
CM5_1V8: C92.1, C93.1, C243.1, U4.29 (VDDIO), U4.33 (VDDIO)
CM5_3V3: C30.2, FB21.2, FB22.1, R66.1, U4.2 (VDD_3V3)
ETH.0_N: TP70.1, U4.15 (ETH0_N)
ETH.0_P: TP69.1, U4.14 (ETH0_P)
ETH.1_N: TP71.1, U4.18 (ETH1_N)
ETH.1_P: TP72.1, U4.17 (ETH1_P)
ETH.2_N: TP74.1, U4.21 (VDD_PLL)
ETH.2_P: TP73.1, U4.20 (ETH2_P)
ETH.3_N: TP76.1, U4.23 (ETH3_N)
ETH.3_P: TP75.1, U4.24 (ETH3_P)
ETH_SYNC_OUT: U4.1 (ETH_SYNC)
ETH_nLED2: U4.43 (LED2)
ETH_nLED3: U4.42 (LED3)
GND: C30.1, C70.1, C71.1, C92.2, C93.2, C94.2, C237.1, C238.2, C239.1, C240.1, C241.1, C242.1, C243.2, R36.1, R69.1, U4.5 (GND), U4.7 (GND), U4.40 (GND), U4.49 (GND), Y3.2, Y3.4
MDIO.INT: R36.2, U4.45 (INT_B)
MDIO.MDC: U4.47 (MDC)
MDIO.MDIO: R66.2, U4.46 (MDIO)
MDIO.RESET: U4.41 (RESET_B)
unnamed: C71.2, FB20.1, TP64.1, U4.3 (VREG)
unnamed: C237.2, R78.1, Y3.3
unnamed: C238.1, U4.9 (OSC), Y3.1
unnamed: C239.2, FB21.1, U4.11 (VDD_PLL2)
unnamed: C94.1, C240.2, FB20.2, U4.10 (VCORE), U4.13 (VCORE), U4.19 (VCORE)
unnamed: C70.2, C241.2, C242.2, FB22.2, U4.16 (VDD_PLL), U4.21 (VDD_PLL), U4.22 (VDD_PLL)
unnamed: R69.2, U4.12 (RBIAS)
unnamed: R78.2, U4.8 (OSC)
RGMII.RXC: U4.39 (RXC)
RGMII.RXD0: U4.35 (RXDn)
RGMII.RXD1: U4.36 (RXDn)
RGMII.RXD2: U4.37 (RXDn)
RGMII.RXD3: U4.38 (RXDn)
RGMII.RX_CTL: U4.34 (RX_CTL)
RGMII.TXC: U4.32 (TXC)
RGMII.TXD0: U4.27 (TXDn)
RGMII.TXD1: U4.28 (TXDn)
RGMII.TXD2: U4.30 (TXDn)
RGMII.TXD3: U4.31 (TXDn)
RGMII.TX_CTL: U4.26 (TX_CTL)
