schlae/cm5-reveng/HDMI.kicad_sch

## KiCad design HDMI.kicad_sch (2025-08-24)

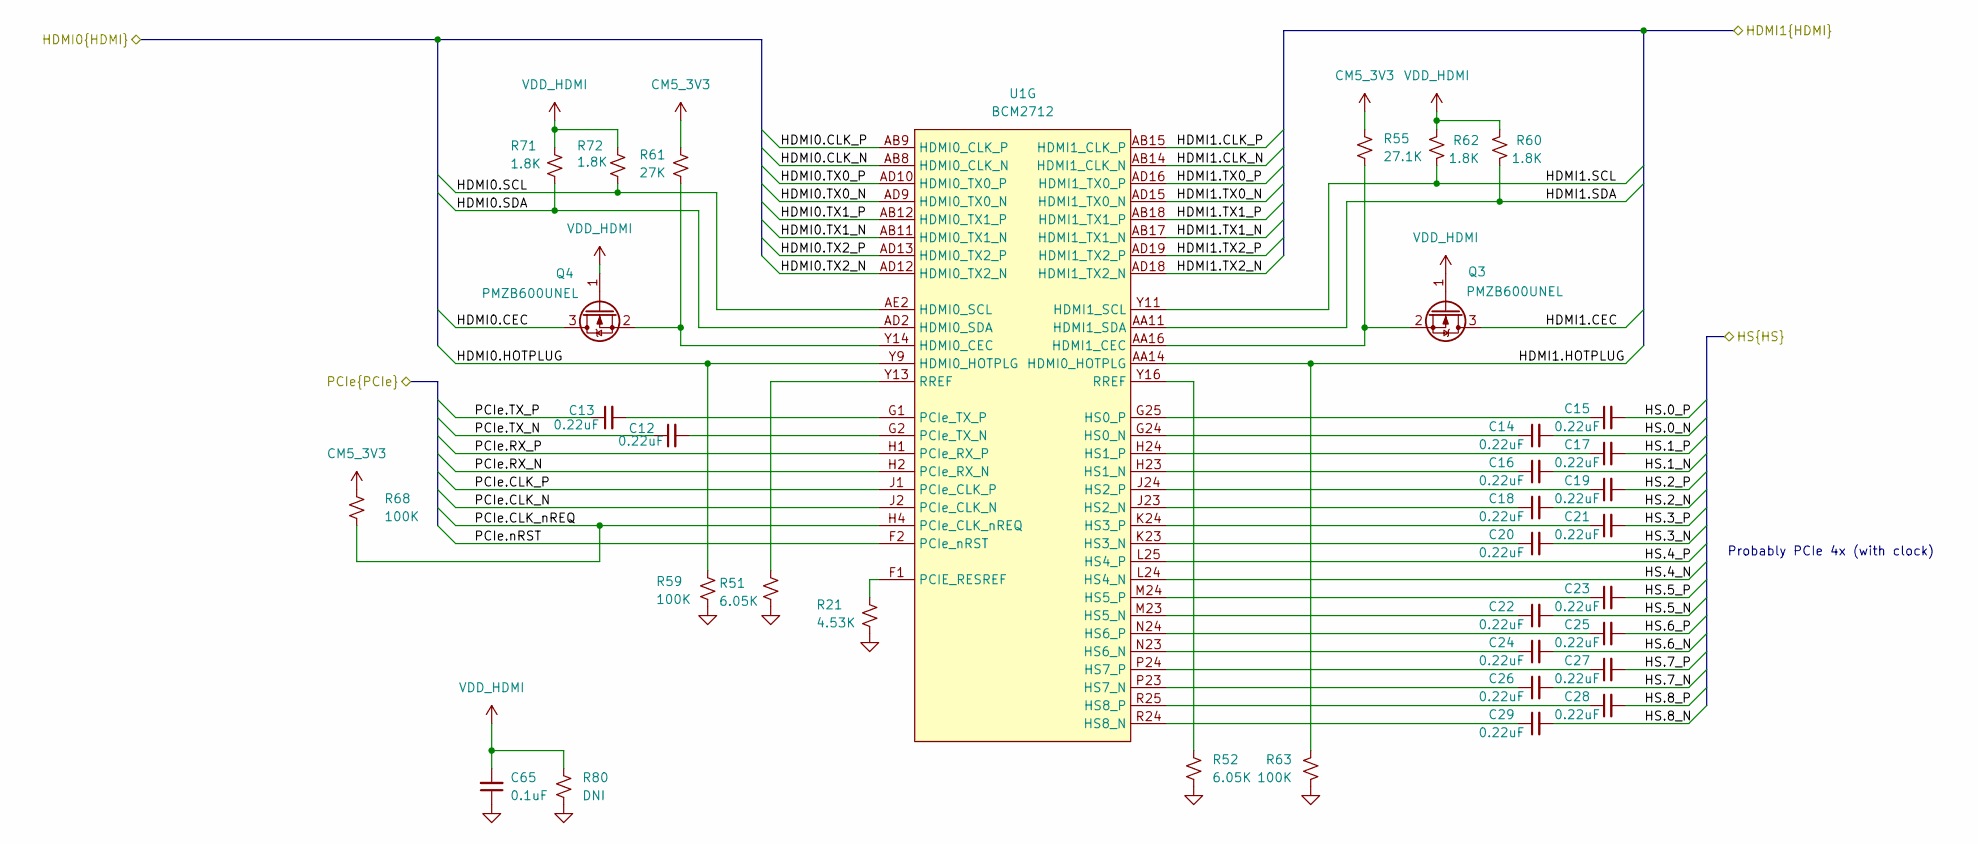
[picture p25: schematic HDMI.kicad_sch]

Parts:
C12, C13, C14, C15, C16, C17, C18, C19, C20, C21, C22, C23, C24, C25, C26, C27, C28, C29: 0.22uF; C_0201_0603Metric
C65: 0.1uF; C_0201_0603Metric
Q3, Q4: PMZB600UNEL; FEMTO_FET
R21: 4.53K; R_0201_0603Metric
R51, R52: 6.05K; R_0201_0603Metric
R55: 27.1K; R_0201_0603Metric
R59, R63, R68: 100K; R_0201_0603Metric
R60, R62, R71, R72: 1.8K; R_0201_0603Metric
R61: 27K; R_0201_0603Metric
R80: DNI; R_0201_0603Metric
U1: BCM2712; BGA-586_25x25_17.0x17.0mm

Connections:
CM5_3V3: R55.2, R61.2, R68.2
GND: C65.1, R21.2, R51.2, R52.1, R59.1, R63.2, R80.2
HDMI0.CEC: Q4.3 (D)
HDMI0.CLK_N: U1.AB8 (HDMI0_CLK_N)
HDMI0.CLK_P: U1.AB9 (HDMI0_CLK_P)
HDMI0.HOTPLUG: R59.2, U1.Y9 (HDMI0_HOTPLG)
HDMI0.SCL: R72.2, U1.AE2 (HDMI0_SCL)
HDMI0.SDA: R71.2, U1.AD2 (HDMI0_SDA)
HDMI0.TX0_N: U1.AD9 (HDMI0_TX0_N)
HDMI0.TX0_P: U1.AD10 (HDMI0_TX0_P)
HDMI0.TX1_N: U1.AB11 (HDMI0_TX1_N)
HDMI0.TX1_P: U1.AB12 (HDMI0_TX1_P)
HDMI0.TX2_N: U1.AD12 (HDMI0_TX2_N)
HDMI0.TX2_P: U1.AD13 (HDMI0_TX2_P)
HDMI1.CEC: Q3.3 (D)
HDMI1.CLK_N: U1.AB14 (HDMI1_CLK_N)
HDMI1.CLK_P: U1.AB15 (HDMI1_CLK_P)
HDMI1.HOTPLUG: R63.1, U1.AA14 (HDMI0_HOTPLG)
HDMI1.SCL: R62.2, U1.Y11 (HDMI1_SCL)
HDMI1.SDA: R60.1, U1.AA11 (HDMI1_SDA)
HDMI1.TX0_N: U1.AD15 (HDMI1_TX0_N)
HDMI1.TX0_P: U1.AD16 (HDMI1_TX0_P)
HDMI1.TX1_N: U1.AB17 (HDMI1_TX1_N)
HDMI1.TX1_P: U1.AB18 (HDMI1_TX1_P)
HDMI1.TX2_N: U1.AD18 (HDMI1_TX2_N)
HDMI1.TX2_P: U1.AD19 (HDMI1_TX2_P)
HS.0_N: C14.2
HS.0_P: C15.2
HS.1_N: C16.2
HS.1_P: C17.2
HS.2_N: C18.2
HS.2_P: C19.2
HS.3_N: C20.2
HS.3_P: C21.2
HS.4_N: U1.L24 (HS4_N)
HS.4_P: U1.L25 (HS4_P)
HS.5_N: C22.2
HS.5_P: C23.2
HS.6_N: C24.2
HS.6_P: C25.2
HS.7_N: C26.2
HS.7_P: C27.2
HS.8_N: C29.2
HS.8_P: C28.2
unnamed: C12.2, U1.G2 (PCIe_TX_N)
unnamed: C13.2, U1.G1 (PCIe_TX_P)
unnamed: C14.1, U1.G24 (HS0_N)
unnamed: C15.1, U1.G25 (HS0_P)
unnamed: C16.1, U1.H23 (HS1_N)
unnamed: C17.1, U1.H24 (HS1_P)
unnamed: C18.1, U1.J23 (HS2_N)
unnamed: C19.1, U1.J24 (HS2_P)
unnamed: C20.1, U1.K23 (HS3_N)
unnamed: C21.1, U1.K24 (HS3_P)
unnamed: C22.1, U1.M23 (HS5_N)
unnamed: C23.1, U1.M24 (HS5_P)
unnamed: C24.1, U1.N23 (HS6_N)
unnamed: C25.1, U1.N24 (HS6_P)
unnamed: C26.1, U1.P23 (HS7_N)
unnamed: C27.1, U1.P24 (HS7_P)
unnamed: C28.1, U1.R25 (HS8_P)
unnamed: C29.1, U1.R24 (HS8_N)
unnamed: Q3.2 (S), R55.1, U1.AA16 (HDMI1_CEC)
unnamed: Q4.2 (S), R61.1, U1.Y14 (HDMI0_CEC)
unnamed: R21.1, U1.F1 (PCIE_RESREF)
unnamed: R51.1, U1.Y13 (RREF)
unnamed: R52.2, U1.Y16 (RREF)
PCIe.CLK_N: U1.J2 (PCIe_CLK_N)
PCIe.CLK_P: U1.J1 (PCIe_CLK_P)
PCIe.CLK_nREQ: R68.1, U1.H4 (PCIe_CLK_nREQ)
PCIe.RX_N: U1.H2 (PCIe_RX_N)
PCIe.RX_P: U1.H1 (PCIe_RX_P)
PCIe.TX_N: C12.1
PCIe.TX_P: C13.1
PCIe.nRST: U1.F2 (PCIe_nRST)
VDD_HDMI: C65.2, Q3.1 (G), Q4.1 (G), R60.2, R62.1, R71.1, R72.1, R80.1

Notes on the sheet:
Probably PCIe 4x (with clock)
