schlae/cm5-reveng/PMIC-RTC.kicad_sch

## KiCad design PMIC-RTC.kicad_sch (2025-08-24)

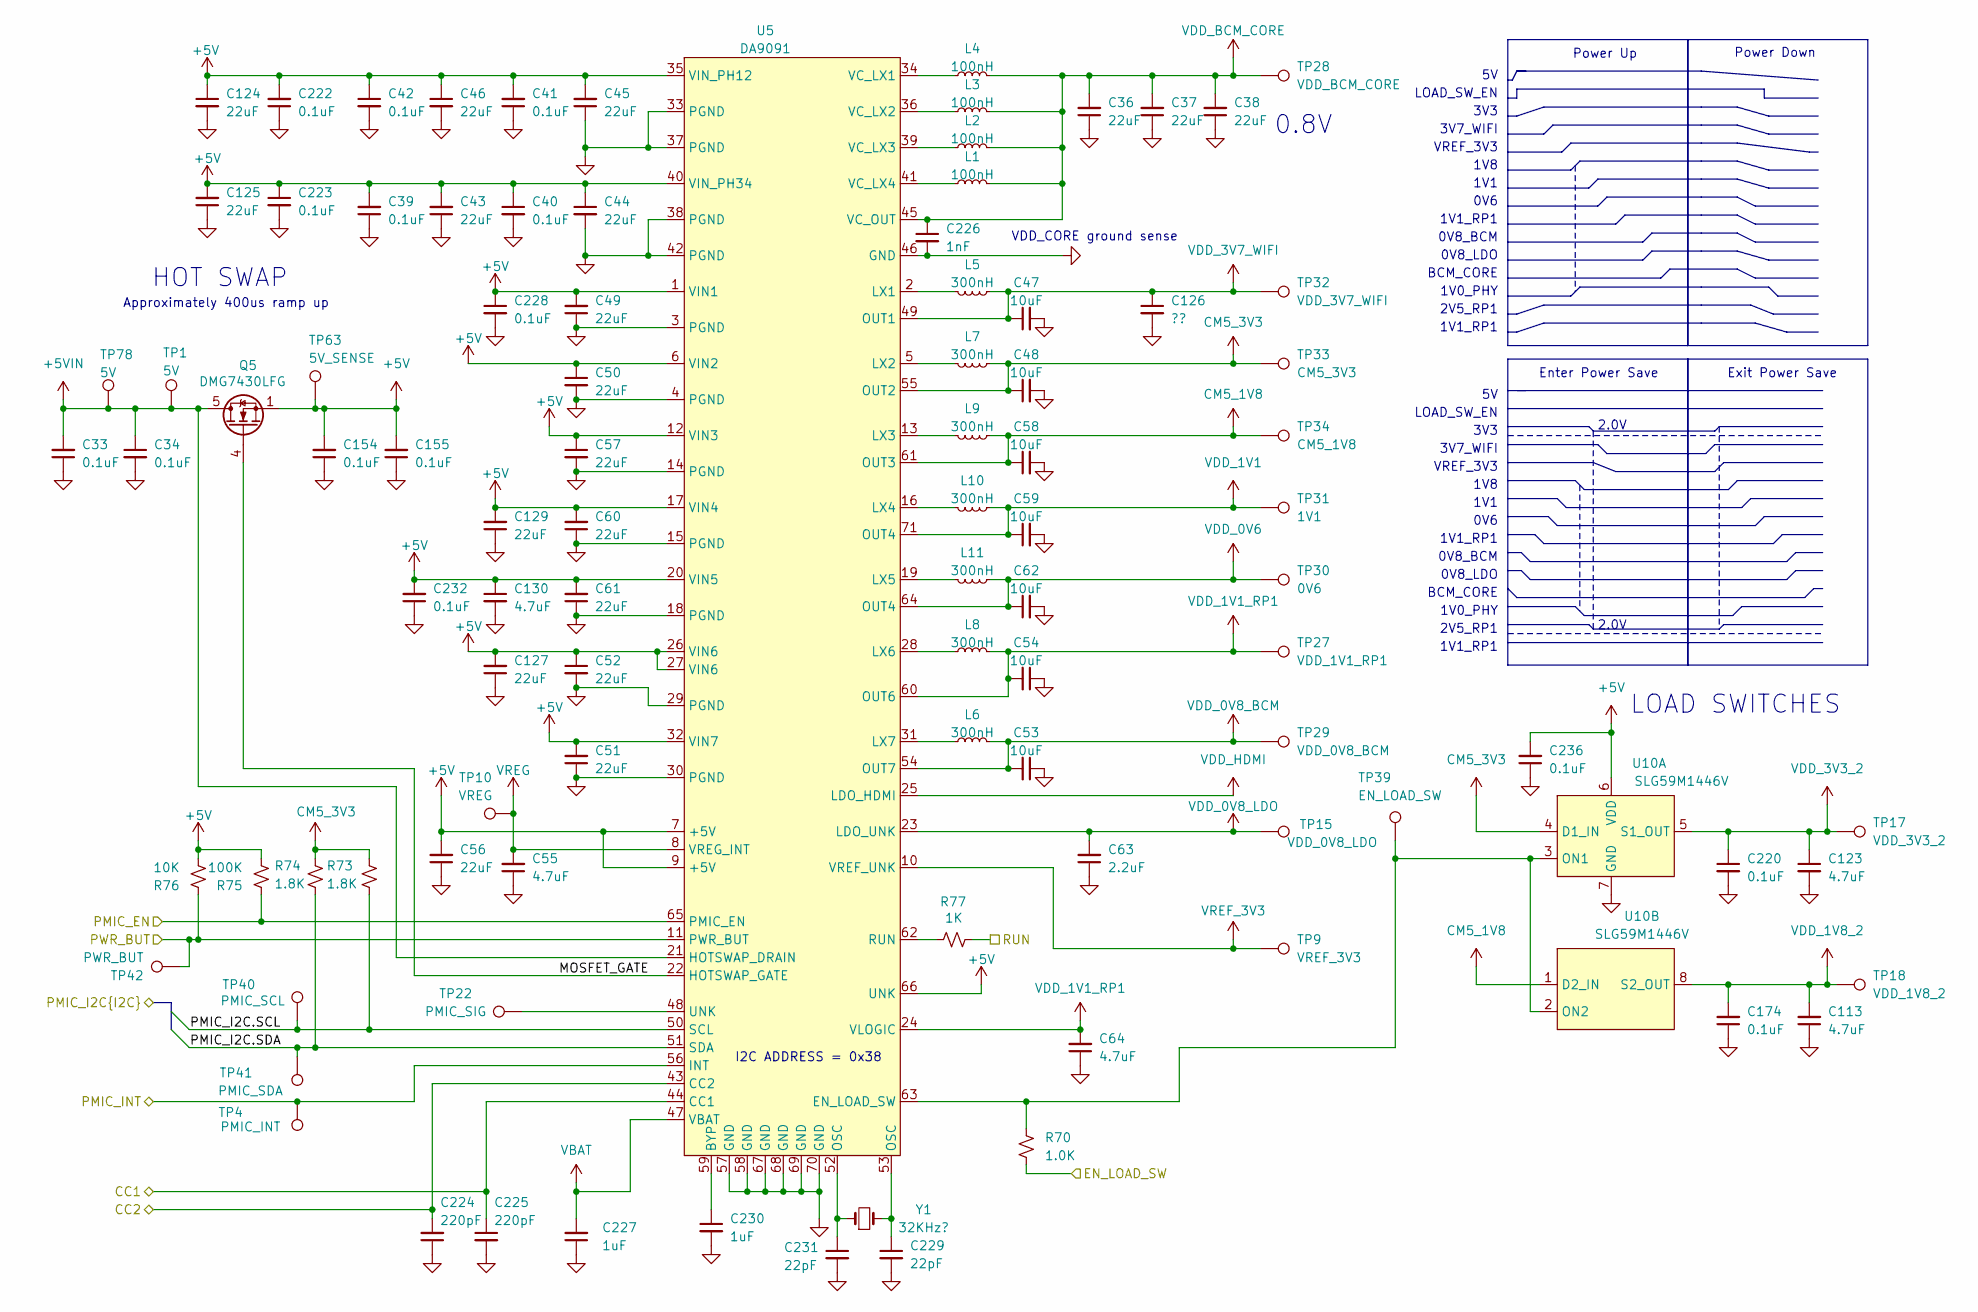
[picture p26: schematic PMIC-RTC.kicad_sch]

Parts:
C33, C34, C39, C40, C41, C42, C154, C155, C174, C220, C222, C223, C228, C232, C236: 0.1uF; C_0201_0603Metric
C36, C37, C38: 22uF; C_0603_1608Metric
C43, C44, C45, C46, C49, C50, C51, C52, C56, C57, C60, C61, C124, C125, C127, C129: 22uF; C_0402_1005Metric
C47, C48, C53, C54, C58, C59, C62: 10uF; C_0402_1005Metric
C55, C64, C113, C123, C130: 4.7uF; C_0402_1005Metric
C63: 2.2uF; C_0402_1005Metric
C126: ??; C_0402_1005Metric
C224, C225: 220pF; C_0201_0603Metric
C226: 1nF; C_0201_0603Metric
C227, C230: 1uF; C_0201_0603Metric
C229, C231: 22pF; C_0201_0603Metric
L1, L2, L3, L4: 100nH; L_1008_2520Metric
L5, L6, L7, L8, L9, L10, L11: 300nH; L_0603_1608Metric
Q5: DMG7430LFG; VSON-8_3.3x3.3mm_P0.65mm_NexFET
R70: 1.0K; R_0201_0603Metric
R73, R74: 1.8K; R_0201_0603Metric
R75: 100K; R_0201_0603Metric
R76: 10K; R_0201_0603Metric
R77: 1K; R_0201_0603Metric
TP1, TP78: 5V; TestPoint_Pad_D1.0mm
TP4: PMIC_INT; TestPoint_Pad_D1.0mm
TP9: VREF_3V3; TestPoint_Pad_D1.0mm
TP10: VREG; TestPoint_Pad_D1.0mm
TP15: VDD_0V8_LDO; TestPoint_Pad_D1.0mm
TP17: VDD_3V3_2; TestPoint_Pad_D1.0mm
TP18: VDD_1V8_2; TestPoint_Pad_D1.0mm
TP22: PMIC_SIG; TestPoint_Pad_D1.0mm
TP27: VDD_1V1_RP1; TestPoint_Pad_D1.0mm
TP28: VDD_BCM_CORE; TestPoint_Pad_D1.0mm
TP29: VDD_0V8_BCM; TestPoint_Pad_D1.0mm
TP30: 0V6; TestPoint_Pad_D1.0mm
TP31: 1V1; TestPoint_Pad_D1.0mm
TP32: VDD_3V7_WIFI; TestPoint_Pad_D1.0mm
TP33: CM5_3V3; TestPoint_Pad_D1.0mm
TP34: CM5_1V8; TestPoint_Pad_D1.0mm
TP39: EN_LOAD_SW; TestPoint_Pad_D1.0mm
TP40: PMIC_SCL; TestPoint_Pad_D1.0mm
TP41: PMIC_SDA; TestPoint_Pad_D1.0mm
TP42: PWR_BUT; TestPoint_Pad_D1.0mm
TP63: 5V_SENSE; TestPoint_Pad_D1.0mm
U5: DA9091; QFN-71_6x6_Pitch0.4mm_Special
U10: SLG59M1446V; STDFN-8
Y1: 32KHz?; Crystal_SMD_2012-2Pin_2.0x1.2mm

Connections:
+5V: C39.2, C40.1, C41.2, C42.1, C43.2, C44.1, C45.2, C46.1, C49.2, C50.1, C51.2, C52.1, C56.2, C57.1, C60.2, C61.2, C124.1, C125.2, C127.2, C129.2, C130.1, C154.2, C155.2, C222.2, C223.1, C228.1, C232.2, C236.2, Q5.1 (S), Q5.2 (S), Q5.3 (S), R75.2, R76.2, TP63.1, U5.1 (VIN1), U5.6 (VIN2), U5.7 (+5V), U5.9 (+5V), U5.12 (VIN3), U5.17 (VIN4), U5.20 (VIN5), U5.26 (VIN6), U5.27 (VIN6), U5.32 (VIN7), U5.35 (VIN_PH12), U5.40 (VIN_PH34), U5.66 (UNK), U10.6 (VDD)
+5VIN: C33.2, C34.1, Q5.5 (D), TP1.1, TP78.1, U5.21 (HOTSWAP_DRAIN)
CC1: C225.1, U5.44 (CC1)
CC2: C224.2, U5.43 (CC2)
CM5_1V8: C58.1, L9.1, TP34.1, U5.61 (OUT3), U10.1 (D2_IN)
CM5_3V3: C48.1, L7.1, R73.2, R74.1, TP33.1, U5.55 (OUT2), U10.4 (D1_IN)
EN_LOAD_SW: R70.2
GND: C33.1, C34.2, C36.1, C37.1, C38.1, C39.1, C40.2, C41.1, C42.2, C43.1, C44.2, C45.1, C46.2, C47.2, C48.2, C49.1, C50.2, C51.1, C52.2, C53.1, C54.1, C55.1, C56.1, C57.2, C58.2, C59.2, C60.1, C61.1, C62.2, C63.1, C64.1, C113.1, C123.2, C124.2, C125.1, C126.2, C127.1, C129.1, C130.2, C154.1, C155.1, C174.1, C220.2, C222.1, C223.2, C224.1, C225.2, C226.2, C227.1, C228.2, C229.2, C230.2, C231.2, C232.1, C236.1, U5.3 (PGND), U5.4 (PGND), U5.14 (PGND), U5.15 (PGND), U5.18 (PGND), U5.29 (PGND), U5.30 (PGND), U5.33 (PGND), U5.37 (PGND), U5.38 (PGND), U5.42 (PGND), U5.46 (GND), U5.57 (GND), U5.58 (GND), U5.67 (GND), U5.68 (GND), U5.69 (GND), U5.70 (GND), U10.7 (GND)
MOSFET_GATE: Q5.4 (G), U5.22 (HOTSWAP_GATE)
unnamed: C229.1, U5.53 (OSC), Y1.2
unnamed: C230.1, U5.59 (BYP)
unnamed: C231.1, U5.52 (OSC), Y1.1
unnamed: L1.1, U5.41 (VC_LX4)
unnamed: L2.1, U5.39 (VC_LX3)
unnamed: L3.1, U5.36 (VC_LX2)
unnamed: L4.1, U5.34 (VC_LX1)
unnamed: L5.2, U5.2 (LX1)
unnamed: L6.1, U5.31 (LX7)
unnamed: L7.2, U5.5 (LX2)
unnamed: L8.1, U5.28 (LX6)
unnamed: L9.2, U5.13 (LX3)
unnamed: L10.2, U5.16 (LX4)
unnamed: L11.2, U5.19 (LX5)
unnamed: R70.1, TP39.1, U5.63 (EN_LOAD_SW), U10.2 (ON2), U10.3 (ON1)
unnamed: R77.2, U5.62 (RUN)
unnamed: TP22.1, U5.48 (UNK)
PMIC_EN: R75.1, U5.65 (PMIC_EN)
PMIC_I2C.SCL: R73.1, TP40.1, U5.50 (SCL)
PMIC_I2C.SDA: R74.2, TP41.1, U5.51 (SDA)
PMIC_INT: TP4.1, U5.56 (INT)
PWR_BUT: R76.1, TP42.1, U5.11 (PWR_BUT)
RUN: R77.1
VBAT: C227.2, U5.47 (VBAT)
VDD_0V6: C62.1, L11.1, TP30.1, U5.64 (OUT4)
VDD_0V8_BCM: C53.2, L6.2, TP29.1, U5.54 (OUT7)
VDD_0V8_LDO: C63.2, TP15.1, U5.23 (LDO_UNK)
VDD_1V1: C59.1, L10.1, TP31.1, U5.71 (OUT4)
VDD_1V1_RP1: C54.2, C64.2, L8.2, TP27.1, U5.24 (VLOGIC), U5.60 (OUT6)
VDD_1V8_2: C113.2, C174.2, TP18.1, U10.8 (S2_OUT)
VDD_3V3_2: C123.1, C220.1, TP17.1, U10.5 (S1_OUT)
VDD_3V7_WIFI: C47.1, C126.1, L5.1, TP32.1, U5.49 (OUT1)
VDD_BCM_CORE: C36.2, C37.2, C38.2, C226.1, L1.2, L2.2, L3.2, L4.2, TP28.1, U5.45 (VC_OUT)
VDD_HDMI: U5.25 (LDO_HDMI)
VREF_3V3: TP9.1, U5.10 (VREF_UNK)
VREG: C55.2, TP10.1, U5.8 (VREG_INT)

Notes on the sheet:
0V6
0V8_LDO
HOT SWAP
3V3
LOAD_SW_EN
Power Up
1V1_RP1
2V5_RP1
Approximately 400us ramp up
2.0V
1V1
LOAD SWITCHES
Enter Power Save
I2C ADDRESS = 0x38
1V0_PHY
1V8
VREF_3V3
BCM_CORE
3V7_WIFI
0.8V
Exit Power Save
0V8_BCM
VDD_CORE ground sense
Power Down
