schlae/cm5-reveng/RP1_IO.kicad_sch

## KiCad design RP1_IO.kicad_sch (2025-08-24)

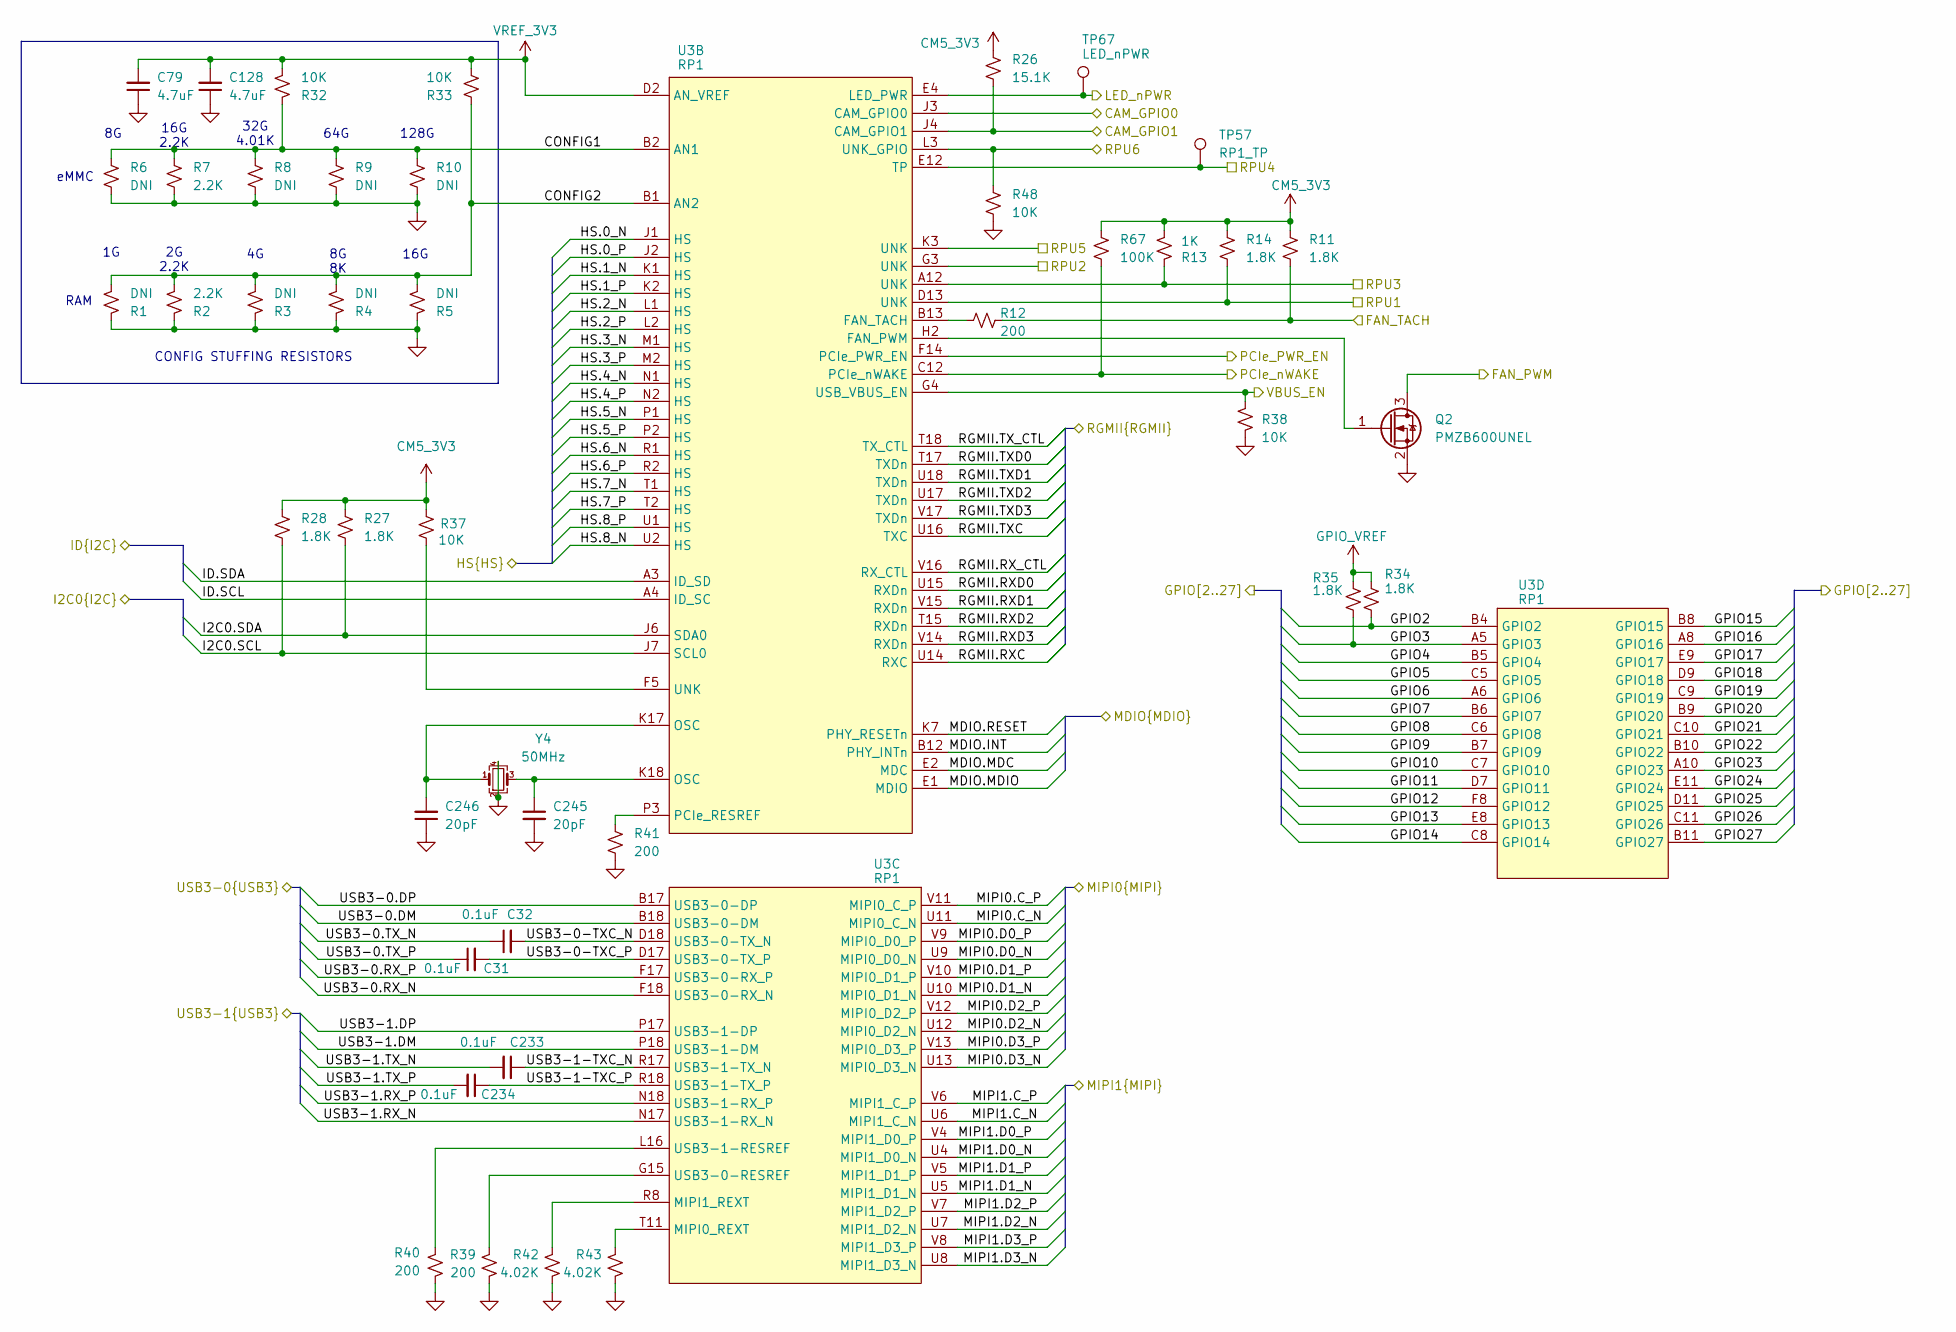
[picture p27: schematic RP1_IO.kicad_sch]

Parts:
C31, C32, C233, C234: 0.1uF; C_0201_0603Metric
C79, C128: 4.7uF; C_0402_1005Metric
C245, C246: 20pF; C_0201_0603Metric
Q2: PMZB600UNEL; FEMTO_FET
R1, R3, R4, R5, R6, R8, R9, R10: DNI; R_0402_1005Metric
R2, R7: 2.2K; R_0402_1005Metric
R11, R14, R27, R28, R34, R35: 1.8K; R_0201_0603Metric
R12, R39, R40, R41: 200; R_0201_0603Metric
R13: 1K; R_0201_0603Metric
R26: 15.1K; R_0201_0603Metric
R32, R33, R37, R38, R48: 10K; R_0201_0603Metric
R42, R43: 4.02K; R_0201_0603Metric
R67: 100K; R_0201_0603Metric
TP57: RP1_TP; TestPoint_Pad_D1.0mm
TP67: LED_nPWR; TestPoint_Pad_D1.0mm
U3: RP1; TFBGA-265_12x12mm_Layout18x18_P0.65mm
Y4: 50MHz; Oscillator_SMD_Abracon_ASCO-4Pin_1.6x1.2mm

Connections:
CAM_GPIO0: U3.J3 (CAM_GPIO0)
CAM_GPIO1: R26.1, U3.J4 (CAM_GPIO1)
CM5_3V3: R11.2, R13.2, R14.2, R26.2, R27.2, R28.2, R37.2, R67.1
CONFIG1: R6.1, R7.1, R8.1, R9.1, R10.1, R32.1, U3.B2 (AN1)
CONFIG2: R1.2, R2.2, R3.2, R4.2, R5.2, R33.1, U3.B1 (AN2)
FAN_PWM: Q2.3 (D)
FAN_TACH: R11.1, R12.2
GND: C79.1, C128.1, C245.2, C246.1, Q2.2 (S), R1.1, R2.1, R3.1, R4.1, R5.1, R6.2, R7.2, R8.2, R9.2, R10.2, R38.2, R39.2, R40.1, R41.1, R42.2, R43.2, R48.1, Y4.2, Y4.4
GPIO2: R34.1, U3.B4 (GPIO2)
GPIO3: R35.1, U3.A5 (GPIO3)
GPIO4: U3.B5 (GPIO4)
GPIO5: U3.C5 (GPIO5)
GPIO6: U3.A6 (GPIO6)
GPIO7: U3.B6 (GPIO7)
GPIO8: U3.C6 (GPIO8)
GPIO9: U3.B7 (GPIO9)
GPIO10: U3.C7 (GPIO10)
GPIO11: U3.D7 (GPIO11)
GPIO12: U3.F8 (GPIO12)
GPIO13: U3.E8 (GPIO13)
GPIO14: U3.C8 (GPIO14)
GPIO15: U3.B8 (GPIO15)
GPIO16: U3.A8 (GPIO16)
GPIO17: U3.E9 (GPIO17)
GPIO18: U3.D9 (GPIO18)
GPIO19: U3.C9 (GPIO19)
GPIO20: U3.B9 (GPIO20)
GPIO21: U3.C10 (GPIO21)
GPIO22: U3.B10 (GPIO22)
GPIO23: U3.A10 (GPIO23)
GPIO24: U3.E11 (GPIO24)
GPIO25: U3.D11 (GPIO25)
GPIO26: U3.C11 (GPIO26)
GPIO27: U3.B11 (GPIO27)
GPIO_VREF: R34.2, R35.2
HS.0_N: U3.J1 (HS)
HS.0_P: U3.J2 (HS)
HS.1_N: U3.K1 (HS)
HS.1_P: U3.K2 (HS)
HS.2_N: U3.L1 (HS)
HS.2_P: U3.L2 (HS)
HS.3_N: U3.M1 (HS)
HS.3_P: U3.M2 (HS)
HS.4_N: U3.N1 (HS)
HS.4_P: U3.N2 (HS)
HS.5_N: U3.P1 (HS)
HS.5_P: U3.P2 (HS)
HS.6_N: U3.R1 (HS)
HS.6_P: U3.R2 (HS)
HS.7_N: U3.T1 (HS)
HS.7_P: U3.T2 (HS)
HS.8_N: U3.U2 (HS)
HS.8_P: U3.U1 (HS)
I2C0.SCL: R28.1, U3.J7 (SCL0)
I2C0.SDA: R27.1, U3.J6 (SDA0)
ID.SCL: U3.A4 (ID_SC)
ID.SDA: U3.A3 (ID_SD)
LED_nPWR: TP67.1, U3.E4 (LED_PWR)
MDIO.INT: U3.B12 (PHY_INTn)
MDIO.MDC: U3.E2 (MDC)
MDIO.MDIO: U3.E1 (MDIO)
MDIO.RESET: U3.K7 (PHY_RESETn)
MIPI0.C_N: U3.U11 (MIPI0_C_N)
MIPI0.C_P: U3.V11 (MIPI0_C_P)
MIPI0.D0_N: U3.U9 (MIPI0_D0_N)
MIPI0.D0_P: U3.V9 (MIPI0_D0_P)
MIPI0.D1_N: U3.U10 (MIPI0_D1_N)
MIPI0.D1_P: U3.V10 (MIPI0_D1_P)
MIPI0.D2_N: U3.U12 (MIPI0_D2_N)
MIPI0.D2_P: U3.V12 (MIPI0_D2_P)
MIPI0.D3_N: U3.U13 (MIPI0_D3_N)
MIPI0.D3_P: U3.V13 (MIPI0_D3_P)
MIPI1.C_N: U3.U6 (MIPI1_C_N)
MIPI1.C_P: U3.V6 (MIPI1_C_P)
MIPI1.D0_N: U3.U4 (MIPI1_D0_N)
MIPI1.D0_P: U3.V4 (MIPI1_D0_P)
MIPI1.D1_N: U3.U5 (MIPI1_D1_N)
MIPI1.D1_P: U3.V5 (MIPI1_D1_P)
MIPI1.D2_N: U3.U7 (MIPI1_D2_N)
MIPI1.D2_P: U3.V7 (MIPI1_D2_P)
MIPI1.D3_N: U3.U8 (MIPI1_D3_N)
MIPI1.D3_P: U3.V8 (MIPI1_D3_P)
unnamed: C245.1, U3.K18 (OSC), Y4.3
unnamed: C246.2, U3.K17 (OSC), Y4.1
unnamed: Q2.1 (G), U3.H2 (FAN_PWM)
unnamed: R12.1, U3.B13 (FAN_TACH)
unnamed: R37.1, U3.F5 (UNK)
unnamed: R39.1, U3.G15 (USB3-0-RESREF)
unnamed: R40.2, U3.L16 (USB3-1-RESREF)
unnamed: R41.2, U3.P3 (PCIe_RESREF)
unnamed: R42.1, U3.R8 (MIPI1_REXT)
unnamed: R43.1, U3.T11 (MIPI0_REXT)
PCIe_PWR_EN: U3.F14 (PCIe_PWR_EN)
PCIe_nWAKE: R67.2, U3.C12 (PCIe_nWAKE)
RGMII.RXC: U3.U14 (RXC)
RGMII.RXD0: U3.U15 (RXDn)
RGMII.RXD1: U3.V15 (RXDn)
RGMII.RXD2: U3.T15 (RXDn)
RGMII.RXD3: U3.V14 (RXDn)
RGMII.RX_CTL: U3.V16 (RX_CTL)
RGMII.TXC: U3.U16 (TXC)
RGMII.TXD0: U3.T17 (TXDn)
RGMII.TXD1: U3.U18 (TXDn)
RGMII.TXD2: U3.U17 (TXDn)
RGMII.TXD3: U3.V17 (TXDn)
RGMII.TX_CTL: U3.T18 (TX_CTL)
RPU1: R14.1, U3.D13 (UNK)
RPU2: U3.G3 (UNK)
RPU3: R13.1, U3.A12 (UNK)
RPU4: TP57.1, U3.E12 (TP)
RPU5: U3.K3 (UNK)
RPU6: R48.2, U3.L3 (UNK_GPIO)
USB3-0-TXC_N: C32.2, U3.D18 (USB3-0-TX_N)
USB3-0-TXC_P: C31.2, U3.D17 (USB3-0-TX_P)
USB3-0.DM: U3.B18 (USB3-0-DM)
USB3-0.DP: U3.B17 (USB3-0-DP)
USB3-0.RX_N: U3.F18 (USB3-0-RX_N)
USB3-0.RX_P: U3.F17 (USB3-0-RX_P)
USB3-0.TX_N: C32.1
USB3-0.TX_P: C31.1
USB3-1-TXC_N: C233.1, U3.R17 (USB3-1-TX_N)
USB3-1-TXC_P: C234.1, U3.R18 (USB3-1-TX_P)
USB3-1.DM: U3.P18 (USB3-1-DM)
USB3-1.DP: U3.P17 (USB3-1-DP)
USB3-1.RX_N: U3.N17 (USB3-1-RX_N)
USB3-1.RX_P: U3.N18 (USB3-1-RX_P)
USB3-1.TX_N: C233.2
USB3-1.TX_P: C234.2
VBUS_EN: R38.1, U3.G4 (USB_VBUS_EN)
VREF_3V3: C79.2, C128.2, R32.2, R33.2, U3.D2 (AN_VREF)

Notes on the sheet:
16G
RAM
2G 2.2K
CONFIG STUFFING RESISTORS
8G 8K
eMMC
32G 4.01K
16G 2.2K
128G
64G
