schlae/cm5-reveng/RP1_POWER.kicad_sch

## KiCad design RP1_POWER.kicad_sch (2025-08-26)

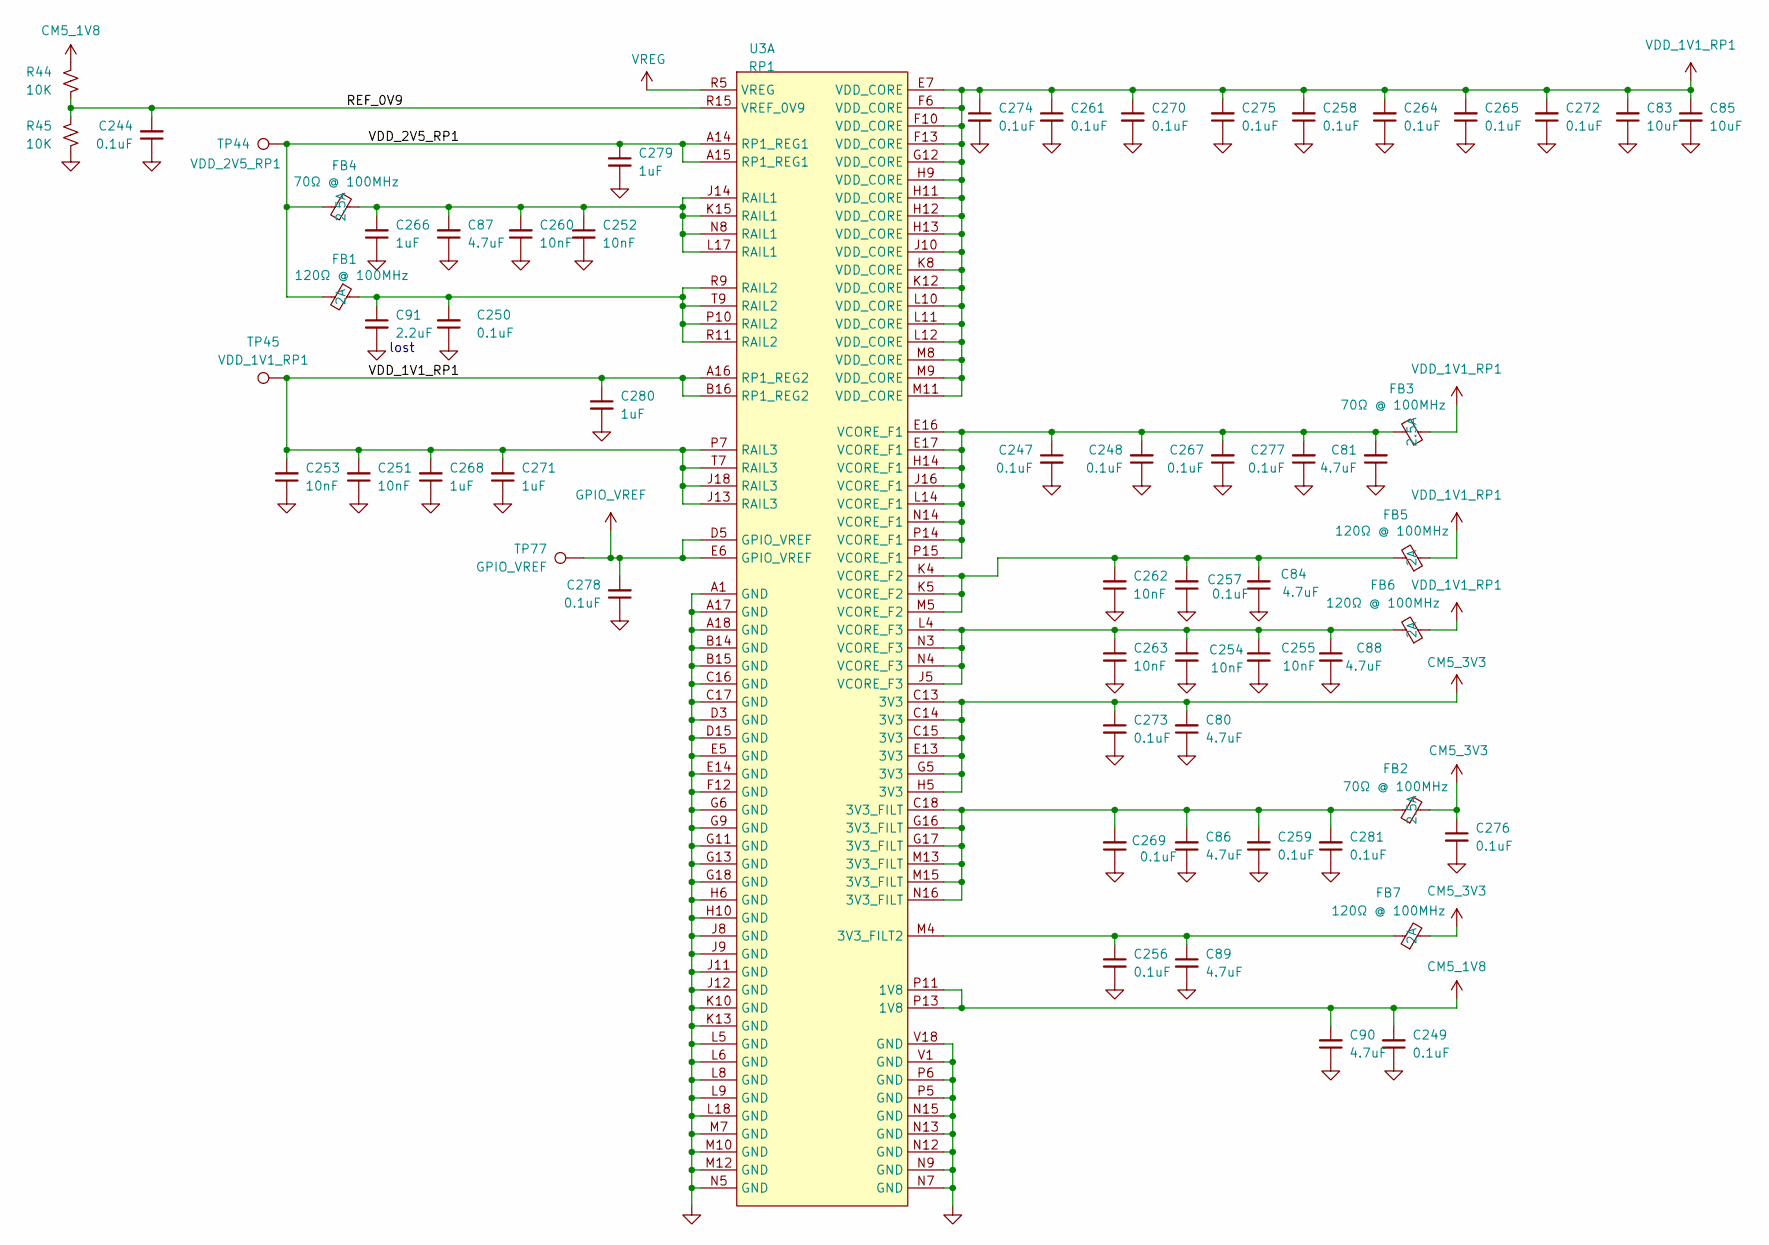
[picture p28: schematic RP1_POWER.kicad_sch]

Parts:
C80, C81, C84, C86, C87, C88, C89, C90: 4.7uF; C_0402_1005Metric
C83, C85: 10uF; C_0402_1005Metric
C91: 2.2uF; C_0402_1005Metric
C244, C247, C248, C249, C250, C256, C258, C259, C261, C262, C264, C265, C267, C269, C270, C272, C273, C274, C275, C276, C277, C278, C281: 0.1uF; C_0201_0603Metric
C251, C252, C253, C254, C255, C257, C260, C263: 10nF; C_0201_0603Metric
C266, C268, C271, C279, C280: 1uF; C_0201_0603Metric
FB1, FB5, FB6, FB7: 120Ω @ 100MHz; L_0402_1005Metric; Rating 2A
FB2, FB3, FB4: 70Ω @ 100MHz; L_0402_1005Metric; Rating 2.5A
R44, R45: 10K; R_0201_0603Metric
TP44: VDD_2V5_RP1; TestPoint_Pad_D1.0mm
TP45: VDD_1V1_RP1; TestPoint_Pad_D1.0mm
TP77: GPIO_VREF; TestPoint_Pad_D1.0mm
U3: RP1; TFBGA-265_12x12mm_Layout18x18_P0.65mm

Connections:
CM5_1V8: C90.2, C249.2, R44.1, U3.P11 (1V8), U3.P13 (1V8)
CM5_3V3: C80.2, C273.1, C276.1, FB2.2, FB7.2, U3.C13 (3V3), U3.C14 (3V3), U3.C15 (3V3), U3.E13 (3V3), U3.G5 (3V3), U3.H5 (3V3)
GND: C80.1, C81.1, C83.1, C84.1, C85.2, C86.1, C87.1, C88.2, C89.2, C90.1, C91.2, C244.1, C247.2, C248.1, C249.1, C250.1, C251.1, C252.2, C253.1, C254.2, C255.2, C256.2, C257.1, C258.1, C259.1, C260.1, C261.2, C262.1, C263.2, C264.1, C265.1, C266.1, C267.1, C268.1, C269.1, C270.2, C271.1, C272.1, C273.2, C274.2, C275.1, C276.2, C277.1, C278.1, C279.2, C280.2, C281.1, R45.1, U3.A1 (GND), U3.A17 (GND), U3.A18 (GND), U3.B14 (GND), U3.B15 (GND), U3.C16 (GND), U3.C17 (GND), U3.D3 (GND), U3.D15 (GND), U3.E5 (GND), U3.E14 (GND), U3.F12 (GND), U3.G6 (GND), U3.G9 (GND), U3.G11 (GND), U3.G13 (GND), U3.G18 (GND), U3.H6 (GND), U3.H10 (GND), U3.J8 (GND), U3.J9 (GND), U3.J11 (GND), U3.J12 (GND), U3.K10 (GND), U3.K13 (GND), U3.L5 (GND), U3.L6 (GND), U3.L8 (GND), U3.L9 (GND), U3.L18 (GND), U3.M7 (GND), U3.M10 (GND), U3.M12 (GND), U3.N5 (GND), U3.N7 (GND), U3.N9 (GND), U3.N12 (GND), U3.N13 (GND), U3.N15 (GND), U3.P5 (GND), U3.P6 (GND), U3.V1 (GND), U3.V18 (GND)
GPIO_VREF: C278.2, TP77.1, U3.D5 (GPIO_VREF), U3.E6 (GPIO_VREF)
unnamed: C81.2, C247.1, C248.2, C267.2, C277.2, FB3.2, U3.E16 (VCORE_F1), U3.E17 (VCORE_F1), U3.H14 (VCORE_F1), U3.J16 (VCORE_F1), U3.L14 (VCORE_F1), U3.N14 (VCORE_F1), U3.P14 (VCORE_F1), U3.P15 (VCORE_F1)
unnamed: C91.1, C250.2, FB1.1, U3.P10 (RAIL2), U3.R9 (RAIL2), U3.R11 (RAIL2), U3.T9 (RAIL2)
unnamed: C87.2, C252.1, C260.2, C266.2, FB4.1, U3.J14 (RAIL1), U3.K15 (RAIL1), U3.L17 (RAIL1), U3.N8 (RAIL1)
unnamed: C88.1, C254.1, C255.1, C263.1, FB6.2, U3.J5 (VCORE_F3), U3.L4 (VCORE_F3), U3.N3 (VCORE_F3), U3.N4 (VCORE_F3)
unnamed: C89.1, C256.1, FB7.1, U3.M4 (3V3_FILT2)
unnamed: C84.2, C257.2, C262.2, FB5.2, U3.K4 (VCORE_F2), U3.K5 (VCORE_F2), U3.M5 (VCORE_F2)
unnamed: C86.2, C259.2, C269.2, C281.2, FB2.1, U3.C18 (3V3_FILT), U3.G16 (3V3_FILT), U3.G17 (3V3_FILT), U3.M13 (3V3_FILT), U3.M15 (3V3_FILT), U3.N16 (3V3_FILT)
REF_0V9: C244.2, R44.2, R45.2, U3.R15 (VREF_0V9)
VDD_1V1_RP1: C83.2, C85.1, C251.2, C253.2, C258.2, C261.1, C264.2, C265.2, C268.2, C270.1, C271.2, C272.2, C274.1, C275.2, C280.1, FB3.1, FB5.1, FB6.1, TP45.1, U3.A16 (RP1_REG2), U3.B16 (RP1_REG2), U3.E7 (VDD_CORE), U3.F6 (VDD_CORE), U3.F10 (VDD_CORE), U3.F13 (VDD_CORE), U3.G12 (VDD_CORE), U3.H9 (VDD_CORE), U3.H11 (VDD_CORE), U3.H12 (VDD_CORE), U3.H13 (VDD_CORE), U3.J10 (VDD_CORE), U3.J13 (RAIL3), U3.J18 (RAIL3), U3.K8 (VDD_CORE), U3.K12 (VDD_CORE), U3.L10 (VDD_CORE), U3.L11 (VDD_CORE), U3.L12 (VDD_CORE), U3.M8 (VDD_CORE), U3.M9 (VDD_CORE), U3.M11 (VDD_CORE), U3.P7 (RAIL3), U3.T7 (RAIL3)
VDD_2V5_RP1: C279.1, FB1.2, FB4.2, TP44.1, U3.A14 (RP1_REG1), U3.A15 (RP1_REG1)
VREG: U3.R5 (VREG)

Notes on the sheet:
lost
