schlae/cm5-reveng/WIFI.kicad_sch

## KiCad design WIFI.kicad_sch (2025-08-24)

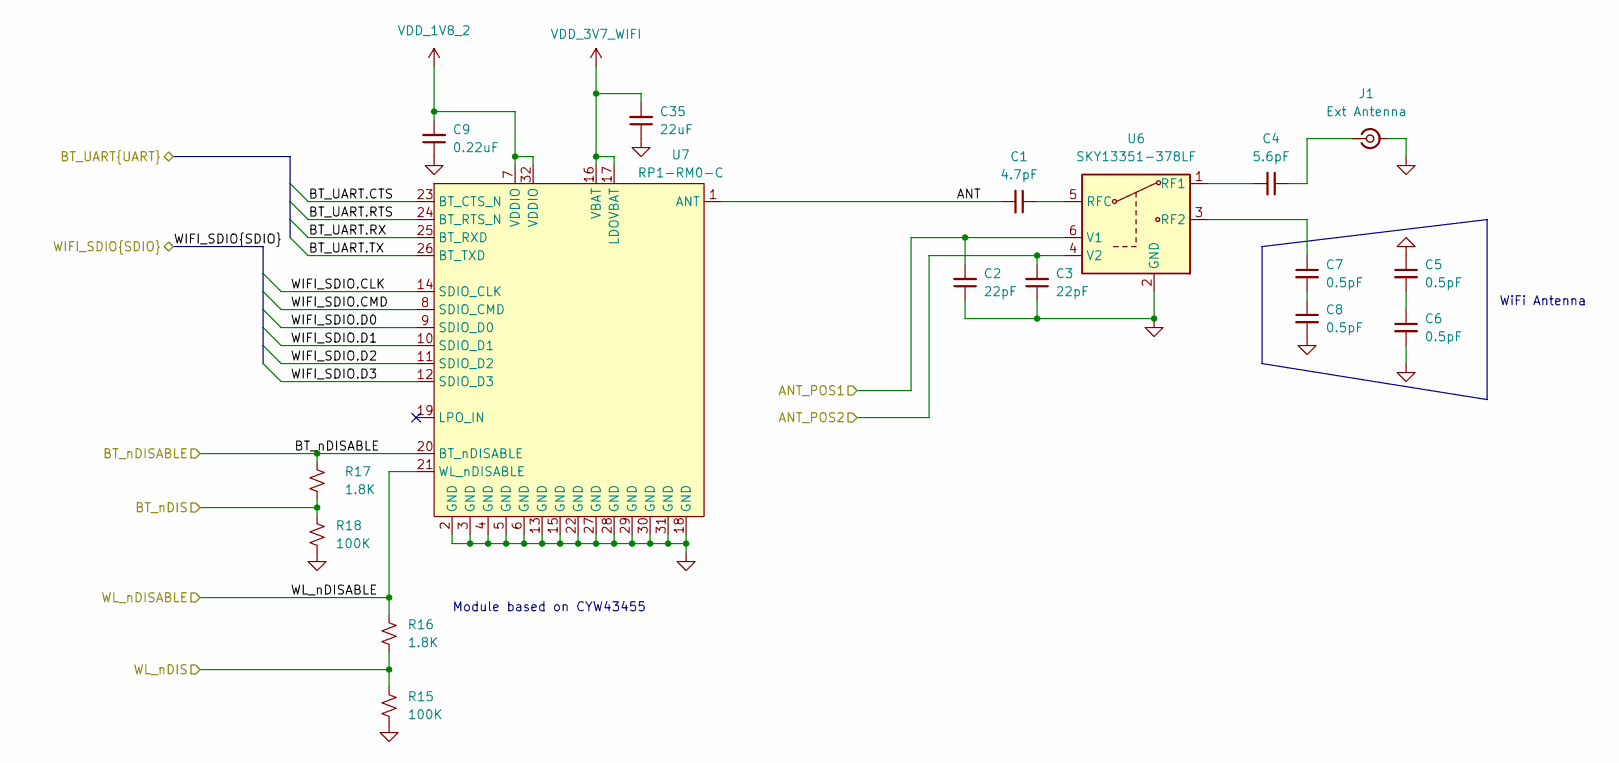
[picture p29: schematic WIFI.kicad_sch]

Parts:
C1: 4.7pF; C_0201_0603Metric
C2, C3: 22pF; C_0201_0603Metric
C4: 5.6pF; C_0201_0603Metric
C5, C6, C7, C8: 0.5pF; C_0201_0603Metric
C9: 0.22uF; C_0201_0603Metric
C35: 22uF; C_0603_1608Metric
J1: Ext Antenna; U.FL_Molex_MCRF_73412-0110_Vertical
R15, R18: 100K; R_0201_0603Metric
R16, R17: 1.8K; R_0201_0603Metric
U6: SKY13351-378LF; DFN-6-1EP_1.2x1.2mm_P0.4mm_EP0.3x0.94mm_PullBack
U7: RP1-RM0-C; RP1-RM0_Module

Connections:
ANT: C1.2, U7.1 (ANT)
ANT_POS1: C2.2, U6.6 (V1)
ANT_POS2: C3.2, U6.4 (V2)
BT_UART.CTS: U7.23 (BT_CTS_N)
BT_UART.RTS: U7.24 (BT_RTS_N)
BT_UART.RX: U7.25 (BT_RXD)
BT_UART.TX: U7.26 (BT_TXD)
BT_nDIS: R17.1, R18.2
BT_nDISABLE: R17.2, U7.20 (BT_nDISABLE)
GND: C2.1, C3.1, C5.1, C6.2, C8.2, C9.1, C35.1, J1.2 (Ext), R15.1, R18.1, U6.2 (GND), U7.2 (GND), U7.3 (GND), U7.4 (GND), U7.5 (GND), U7.6 (GND), U7.13 (GND), U7.15 (GND), U7.18 (GND), U7.22 (GND), U7.27 (GND), U7.28 (GND), U7.29 (GND), U7.30 (GND), U7.31 (GND)
unnamed: C1.1, U6.5 (RFC)
unnamed: C4.1, J1.1 (In)
unnamed: C4.2, U6.1 (RF1)
unnamed: C5.2, C6.1
unnamed: C7.1, U6.3 (RF2)
unnamed: C7.2, C8.1
VDD_1V8_2: C9.2, U7.7 (VDDIO), U7.32 (VDDIO)
VDD_3V7_WIFI: C35.2, U7.16 (VBAT), U7.17 (LDOVBAT)
WIFI_SDIO.CLK: U7.14 (SDIO_CLK)
WIFI_SDIO.CMD: U7.8 (SDIO_CMD)
WIFI_SDIO.D0: U7.9 (SDIO_D0)
WIFI_SDIO.D1: U7.10 (SDIO_D1)
WIFI_SDIO.D2: U7.11 (SDIO_D2)
WIFI_SDIO.D3: U7.12 (SDIO_D3)
WL_nDIS: R15.2, R16.2
WL_nDISABLE: R16.1, U7.21 (WL_nDISABLE)

Notes on the sheet:
Module based on CYW43455
WiFi Antenna
