schlae/cm5-reveng/rpi-rm0/rpi-rm0.kicad_sch

## KiCad design rpi-rm0/rpi-rm0.kicad_sch (2025-08-24)

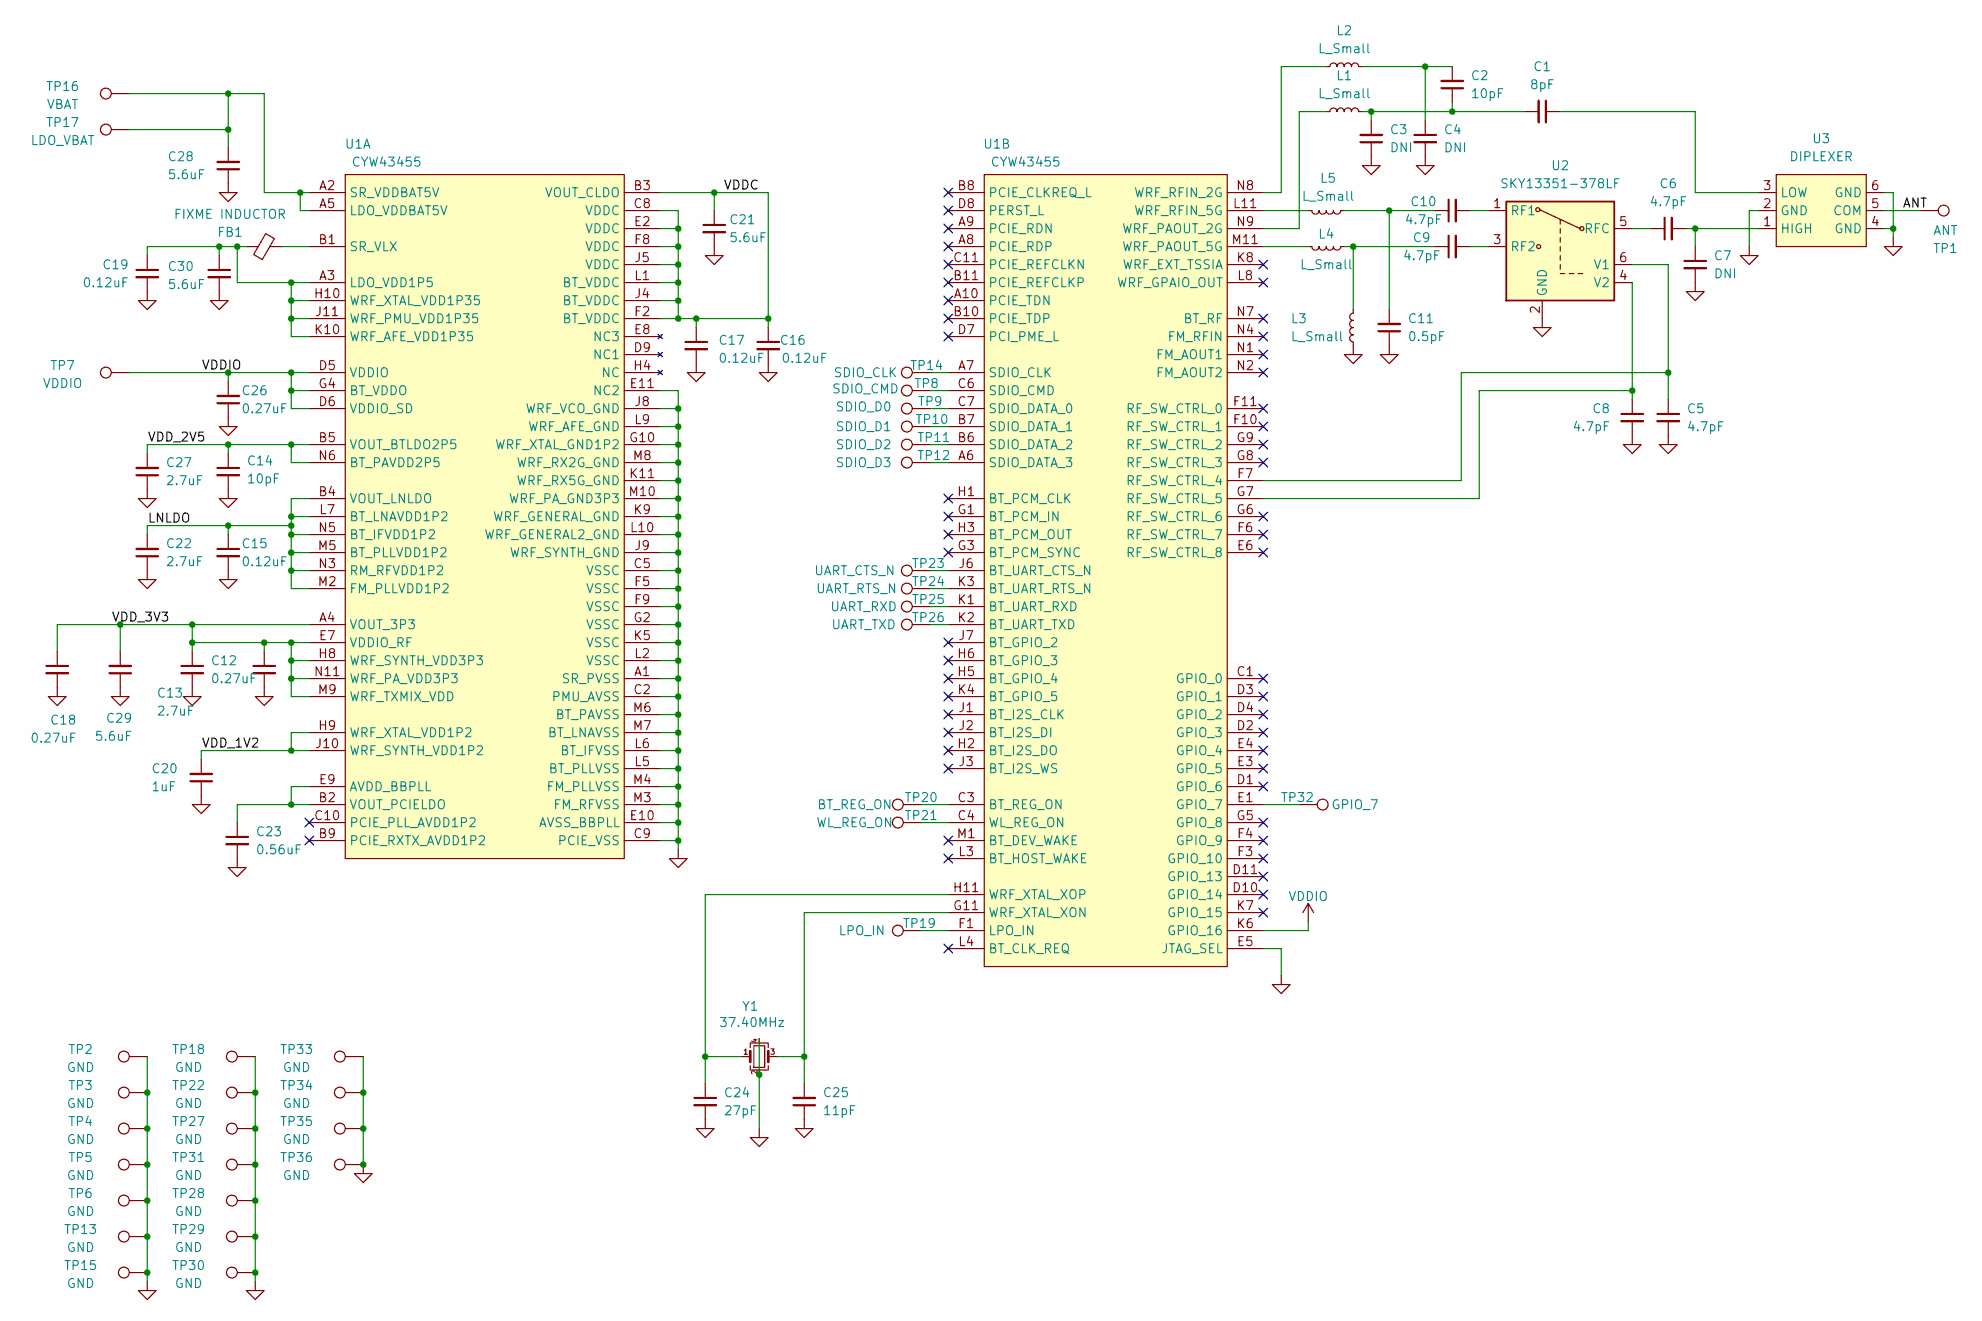
[picture p30: schematic rpi-rm0.kicad_sch]

Parts:
C1: 8pF; C_0201_0603Metric
C2, C14: 10pF; C_0201_0603Metric
C3, C4, C7: DNI; C_0201_0603Metric
C5, C6, C8, C9, C10: 4.7pF; C_0201_0603Metric
C11: 0.5pF; C_0201_0603Metric
C12, C18, C26: 0.27uF; C_0201_0603Metric
C13, C22, C27: 2.7uF; C_0402_1005Metric
C15, C16, C17, C19: 0.12uF; C_0201_0603Metric
C20: 1uF; C_0201_0603Metric
C21, C28, C29, C30: 5.6uF; C_0402_1005Metric
C23: 0.56uF; C_0201_0603Metric
C24: 27pF; C_0201_0603Metric
C25: 11pF; C_0201_0603Metric
FB1: FIXME INDUCTOR; L_0603_1608Metric
L1, L2, L3, L4, L5: L_Small; L_0201_0603Metric
TP1: ANT; Pad07X03
TP2, TP3, TP4, TP5, TP6, TP13, TP15, TP18, TP22, TP27, TP28, TP29, TP30, TP31: GND; Pad07X03
TP7: VDDIO; Pad07X03
TP8: SDIO_CMD; Pad07X03
TP9: SDIO_D0; Pad07X03
TP10: SDIO_D1; Pad07X03
TP11: SDIO_D2; Pad07X03
TP12: SDIO_D3; Pad07X03
TP14: SDIO_CLK; Pad07X03
TP16: VBAT; Pad07X03
TP17: LDO_VBAT; Pad07X03
TP19: LPO_IN; Pad07X03
TP20: BT_REG_ON; Pad07X03
TP21: WL_REG_ON; Pad07X03
TP23: UART_CTS_N; Pad07X03
TP24: UART_RTS_N; Pad07X03
TP25: UART_RXD; Pad07X03
TP26: UART_TXD; Pad07X03
TP32: GPIO_7; Pad1X1
TP33, TP34, TP35, TP36: GND; Pad1X1
U1: CYW43455; BGA-140_11x13_4.47x5.27mm
U2: SKY13351-378LF; DFN-6-1EP_1.2x1.2mm_P0.4mm_EP0.3x0.94mm_PullBack
U3: DIPLEXER; Balun_Johanson_1.6x0.8mm
Y1: 37.40MHz; Crystal_SMD_1210-4Pin_1.2x1.0mm

Connections:
ANT: TP1.1, U3.5 (COM)
GND: C3.1, C4.2, C5.2, C7.2, C8.2, C11.1, C12.2, C13.2, C14.2, C15.2, C16.2, C17.2, C18.2, C19.2, C20.1, C21.2, C22.1, C23.2, C24.2, C25.1, C26.1, C27.1, C28.1, C29.1, C30.2, L3.1, TP2.1, TP3.1, TP4.1, TP5.1, TP6.1, TP13.1, TP15.1, TP18.1, TP22.1, TP27.1, TP28.1, TP29.1, TP30.1, TP31.1, TP33.1, TP34.1, TP35.1, TP36.1, U1.A1 (SR_PVSS), U1.C2 (PMU_AVSS), U1.C5 (VSSC), U1.C9 (PCIE_VSS), U1.E5 (JTAG_SEL), U1.E10 (AVSS_BBPLL), U1.E11 (NC2), U1.F5 (VSSC), U1.F9 (VSSC), U1.G2 (VSSC), U1.G10 (WRF_XTAL_GND1P2), U1.J8 (WRF_VCO_GND), U1.J9 (WRF_SYNTH_GND), U1.K5 (VSSC), U1.K9 (WRF_GENERAL_GND), U1.K11 (WRF_RX5G_GND), U1.L2 (VSSC), U1.L5 (BT_PLLVSS), U1.L6 (BT_IFVSS), U1.L9 (WRF_AFE_GND), U1.L10 (WRF_GENERAL2_GND), U1.M3 (FM_RFVSS), U1.M4 (FM_PLLVSS), U1.M6 (BT_PAVSS), U1.M7 (BT_LNAVSS), U1.M8 (WRF_RX2G_GND), U1.M10 (WRF_PA_GND3P3), U2.2 (GND), U3.2 (GND), U3.4 (GND), U3.6 (GND), Y1.2, Y1.4
LNLDO: C15.1, C22.2, U1.B4 (VOUT_LNLDO), U1.L7 (BT_LNAVDD1P2), U1.M2 (FM_PLLVDD1P2), U1.M5 (BT_PLLVDD1P2), U1.N3 (RM_RFVDD1P2), U1.N5 (BT_IFVDD1P2)
unnamed: C1.1, U3.3 (LOW)
unnamed: C1.2, C2.1, C3.2, L1.2
unnamed: C2.2, C4.1, L2.2
unnamed: C5.1, U1.F7 (RF_SW_CTRL_4), U2.6 (V1)
unnamed: C6.1, U2.5 (RFC)
unnamed: C6.2, C7.1, U3.1 (HIGH)
unnamed: C8.1, U1.G7 (RF_SW_CTRL_5), U2.4 (V2)
unnamed: C9.1, L3.2, L4.1
unnamed: C9.2, U2.3 (RF2)
unnamed: C10.1, C11.2, L5.1
unnamed: C10.2, U2.1 (RF1)
unnamed: C19.1, C30.1, FB1.1, U1.A3 (LDO_VDD1P5), U1.H10 (WRF_XTAL_VDD1P35), U1.J11 (WRF_PMU_VDD1P35), U1.K10 (WRF_AFE_VDD1P35)
unnamed: C23.1, U1.B2 (VOUT_PCIELDO), U1.E9 (AVDD_BBPLL)
unnamed: C24.1, U1.H11 (WRF_XTAL_XOP), Y1.1
unnamed: C25.2, U1.G11 (WRF_XTAL_XON), Y1.3
unnamed: C28.2, TP16.1, TP17.1, U1.A2 (SR_VDDBAT5V), U1.A5 (LDO_VDDBAT5V)
unnamed: FB1.2, U1.B1 (SR_VLX)
unnamed: L1.1, U1.N9 (WRF_PAOUT_2G)
unnamed: L2.1, U1.N8 (WRF_RFIN_2G)
unnamed: L4.2, U1.M11 (WRF_PAOUT_5G)
unnamed: L5.2, U1.L11 (WRF_RFIN_5G)
unnamed: TP8.1, U1.C6 (SDIO_CMD)
unnamed: TP9.1, U1.C7 (SDIO_DATA_0)
unnamed: TP10.1, U1.B7 (SDIO_DATA_1)
unnamed: TP11.1, U1.B6 (SDIO_DATA_2)
unnamed: TP12.1, U1.A6 (SDIO_DATA_3)
unnamed: TP14.1, U1.A7 (SDIO_CLK)
unnamed: TP19.1, U1.F1 (LPO_IN)
unnamed: TP20.1, U1.C3 (BT_REG_ON)
unnamed: TP21.1, U1.C4 (WL_REG_ON)
unnamed: TP23.1, U1.J6 (BT_UART_CTS_N)
unnamed: TP24.1, U1.K3 (BT_UART_RTS_N)
unnamed: TP25.1, U1.K1 (BT_UART_RXD)
unnamed: TP26.1, U1.K2 (BT_UART_TXD)
unnamed: TP32.1, U1.E1 (GPIO_7)
VDDC: C16.1, C17.1, C21.1, U1.B3 (VOUT_CLDO), U1.C8 (VDDC), U1.E2 (VDDC), U1.F2 (BT_VDDC), U1.F8 (VDDC), U1.J4 (BT_VDDC), U1.J5 (VDDC), U1.L1 (BT_VDDC)
VDDIO: C26.2, TP7.1, U1.D5 (VDDIO), U1.D6 (VDDIO_SD), U1.G4 (BT_VDDO), U1.K6 (GPIO_16)
VDD_1V2: C20.2, U1.H9 (WRF_XTAL_VDD1P2), U1.J10 (WRF_SYNTH_VDD1P2)
VDD_2V5: C14.1, C27.2, U1.B5 (VOUT_BTLDO2P5), U1.N6 (BT_PAVDD2P5)
VDD_3V3: C12.1, C13.1, C18.1, C29.2, U1.A4 (VOUT_3P3), U1.E7 (VDDIO_RF), U1.H8 (WRF_SYNTH_VDD3P3), U1.M9 (WRF_TXMIX_VDD), U1.N11 (WRF_PA_VDD3P3)
